meriac/openbeacon-ng/firmware/nRF51/tag-proximity/src/main.c

/***************************************************************
 *
 * OpenBeacon.org - nRF51 Main Entry
 *
 * Copyright 2013 Milosch Meriac <meriac@openbeacon.de>
 *
 ***************************************************************

 This file is part of the OpenBeacon.org active RFID firmware

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
*/
#include <openbeacon.h>

#include <acc.h>
#include <adc.h>
#include <log.h>
#include <radio.h>
#include <timer.h>

static int8_t g_tag_angle;

int8_t tag_angle(void)
{
	return g_tag_angle;
}

static void blink(uint8_t times)
{
	while(times--)
	{
		nrf_gpio_pin_set(CONFIG_LED_PIN);
		timer_wait(MILLISECONDS(1));
		nrf_gpio_pin_clear(CONFIG_LED_PIN);
		timer_wait(MILLISECONDS(499));
	}
}

void halt(uint8_t times)
{
	while(TRUE)
	{
		blink(times);
		timer_wait(SECONDS(3));
	}
}

static void run_mode_beacon(uint32_t tag_id)
{
	int i;
	bool do_blink;

	/* start radio */
	radio_init(tag_id);
	debug_printf("- Start radio\n\r");

	/* power down USART */
	uart_power(FALSE);

	/* turn off LED to indicate operation */
	nrf_gpio_pin_clear(CONFIG_LED_PIN);

	/* enter main loop */
	i = 0;
	do_blink = false;
	while(TRUE)
	{
		/* get tag angle once per second */
		acc_magnitude(&g_tag_angle);
		timer_wait(MILLISECONDS(1000));

		/* process log entries */
		if(log_process())
			do_blink = true;

		/* blink every 5 seconds */
		if(i<5)
			i++;
		else
		{
			i = 0;
			nrf_gpio_pin_set(CONFIG_LED_PIN);
			timer_wait(MILLISECONDS(1));
			nrf_gpio_pin_clear(CONFIG_LED_PIN);

			/* check whether to indicate logging of data */
			if(do_blink)
			{
				do_blink = false;
				timer_wait(MILLISECONDS(100));
				nrf_gpio_pin_set(CONFIG_LED_PIN);
				timer_wait(MILLISECONDS(1));
				nrf_gpio_pin_clear(CONFIG_LED_PIN);
			}
		}
	}
}

void main_entry(void)
{
	int voltage;
	uint32_t tag_id;

	/* enabled LED output */
	nrf_gpio_cfg_output(CONFIG_LED_PIN);
	nrf_gpio_pin_set(CONFIG_LED_PIN);

	/* enabled input pin */
	nrf_gpio_cfg_input(CONFIG_SWITCH_PIN, NRF_GPIO_PIN_NOPULL);

	/* initialize UART */
	uart_init();

	/* start timer */
	timer_init();

	/* calculate tag ID from NRF_FICR->DEVICEID */
	tag_id = crc32((void*)&NRF_FICR->DEVICEID, sizeof(NRF_FICR->DEVICEID));
#if defined(MARKER_TAG_NEAR) || defined(MARKER_TAG_FAR)
	tag_id |= MARKER_TAG_BIT;
#else /*MARKER_TAG*/
	tag_id &= MARKER_TAG_BIT-1;
#endif/*MARKER_TAG*/
	debug_printf("\n\rInitializing Tag[%08X] v" PROGRAM_VERSION " @24%02iMHz ...\n\r",
		tag_id,
		CONFIG_TRACKER_CHANNEL);

	/* initialize ADC battery voltage measurements */
	adc_init();
	voltage = (int)adc_bat_sync() * 100;
	debug_printf("- Supply voltage of %imV\n\r", voltage);

	/* initialize external flash */
	if(log_init(tag_id))
		halt(2);

	/* initialize accelerometer */
	if(acc_init())
		halt(3);

	/* for voltages above 3.2V assume to be in reader */
	if(voltage >= 3200)
		log_dump(tag_id);
	else
		run_mode_beacon(tag_id);
}
