meriac/openbeacon-ng/firmware/nRF51/tag-proximity/src/radio.c

/***************************************************************
 *
 * OpenBeacon.org - nRF51 2.4GHz Radio Routines
 *
 * Copyright 2013 Milosch Meriac <meriac@openbeacon.de>
 *
 ***************************************************************

 This file is part of the OpenBeacon.org active RFID firmware

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
*/
#include <openbeacon.h>
#include <main.h>
#include <radio.h>
#include <adc.h>
#include <aes.h>
#include <rng.h>
#include <log.h>
#include <timer.h>

/* set proximity power */
#ifdef MARKER_TAG_FAR
#  define PX_POWER 4
#  define PX_POWER_VALUE RADIO_TXPOWER_TXPOWER_Pos4dBm
#elif  MARKER_TAG_NEAR
#  define PX_POWER -16
#  define PX_POWER_VALUE RADIO_TXPOWER_TXPOWER_Neg16dBm
#else/*PROX_TAG*/
#  define PROX_TAG
#  define PX_POWER -20
#  define PX_POWER_VALUE RADIO_TXPOWER_TXPOWER_Neg20dBm
#endif/*MARKER_TAG*/

#define RXTX_BASELOSS -4.0
#define BALUN_INSERT_LOSS -2.25
#define BALUN_RETURN_LOSS -10.0
#define ANTENNA_GAIN 0.5
#define RX_LOSS ((RXTX_BASELOSS/2.0)+BALUN_RETURN_LOSS+ANTENNA_GAIN)
#define TX_LOSS ((RXTX_BASELOSS/2.0)+BALUN_INSERT_LOSS+ANTENNA_GAIN)

static volatile uint32_t g_time, g_pkt_tracker_ticks;
static volatile uint16_t g_ticks_offset;
static volatile uint8_t g_request_tx;
static uint8_t g_listen_ratio;
static uint8_t g_nrf_state;
static int8_t g_rssi;
static uint8_t g_button_pressed;

static TBeaconNgProx g_pkt_prox ALIGN4;
static uint8_t g_pkt_prox_enc[sizeof(g_pkt_prox)] ALIGN4;

static TBeaconNgProx g_pkt_prox_rx ALIGN4;
static uint8_t g_pkt_prox_rx_enc[sizeof(g_pkt_prox_rx)] ALIGN4;

static TBeaconNgTracker g_pkt_tracker ALIGN4;
static uint8_t g_pkt_tracker_enc[sizeof(g_pkt_tracker)] ALIGN4;

/* don't start DC/DC converter for voltages below 2.3V */
#define NRF_DCDC_STARTUP_VOLTAGE 23

#define NRF_MAC_SIZE 5UL
#define NRF_PROX_SIZE sizeof(TBeaconNgProx)
#define NRF_TRACKER_SIZE sizeof(TBeaconNgTracker)

#define NRF_STATE_IDLE           0
#define NRF_STATE_TX_PROX        1
#define NRF_STATE_RX_PROX        2
#define NRF_STATE_RX_PROX_PACKET 3
#define NRF_STATE_RX_PROX_BLINK  4
#define NRF_STATE_TX_TRACKER     5

#define RADIO_TRACKER_TXADDRESS 1
#define RADIO_TRACKER_TXPOWER (RADIO_TXPOWER_TXPOWER_Pos4dBm << RADIO_TXPOWER_TXPOWER_Pos)
#define RADIO_TRACKER_PCNF1 \
		(RADIO_PCNF1_WHITEEN_Disabled << RADIO_PCNF1_WHITEEN_Pos) |\
		(RADIO_PCNF1_ENDIAN_Big       << RADIO_PCNF1_ENDIAN_Pos)  |\
		((NRF_MAC_SIZE-1UL)           << RADIO_PCNF1_BALEN_Pos)   |\
		(NRF_TRACKER_SIZE             << RADIO_PCNF1_STATLEN_Pos) |\
		(NRF_TRACKER_SIZE             << RADIO_PCNF1_MAXLEN_Pos)

#define RADIO_PROX_TXADDRESS 0
#define RADIO_PROX_TXPOWER (PX_POWER_VALUE << RADIO_TXPOWER_TXPOWER_Pos)
#define RADIO_PROX_PCNF1 \
		(RADIO_PCNF1_WHITEEN_Enabled  << RADIO_PCNF1_WHITEEN_Pos) |\
		(RADIO_PCNF1_ENDIAN_Big       << RADIO_PCNF1_ENDIAN_Pos)  |\
		((NRF_MAC_SIZE-1UL)           << RADIO_PCNF1_BALEN_Pos)   |\
		(NRF_PROX_SIZE                << RADIO_PCNF1_STATLEN_Pos) |\
		(NRF_PROX_SIZE                << RADIO_PCNF1_MAXLEN_Pos)

void RTC0_IRQ_Handler(void)
{
	uint32_t delta_t;

	/* run every second */
	if(NRF_RTC0->EVENTS_COMPARE[0])
	{
		/* acknowledge event */
		NRF_RTC0->EVENTS_COMPARE[0] = 0;

		/* re-trigger in one second */
		NRF_RTC0->CC[0]+= LF_FREQUENCY;

		/* increment time */
		g_time++;

		/* decrement button timer if needed */
		if(g_button_pressed)
			g_button_pressed--;

		/* schedule tracker TX */
		if(!g_request_tx)
			/* wait for random(2^5) slots */
			g_request_tx = rng(5);

		/* measure battery voltage once per second */
		adc_start();
	}

	if(NRF_RTC0->EVENTS_COMPARE[1])
	{
		/* acknowledge event */
		NRF_RTC0->EVENTS_COMPARE[1] = 0;

		/* re-trigger next RX/TX-slot */
		delta_t =
			CONFIG_PROX_SPACING -
			(1<<(CONFIG_PROX_SPACING_RNG_BITS-1)) +
			rng(CONFIG_PROX_SPACING_RNG_BITS);
		NRF_RTC0->CC[1] = NRF_RTC0->COUNTER + delta_t;

		/* start HF crystal oscillator */
		NRF_CLOCK->TASKS_HFCLKSTART = 1;

#ifdef  PROX_TAG
		/* listen every CONFIG_PROX_LISTEN_RATIO slots */
		g_listen_ratio++;
#endif/*PROX_TAG*/
		if(g_listen_ratio<CONFIG_PROX_LISTEN_RATIO)
			g_nrf_state = NRF_STATE_TX_PROX;
		else
		{
			g_listen_ratio = 0;
			g_nrf_state = NRF_STATE_RX_PROX;

			/* only start DC/DC converter for
			 * RX & higher battery voltages */
			if(adc_bat()>=NRF_DCDC_STARTUP_VOLTAGE)
			{
				/* start DC-DC converter */
				NRF_POWER->DCDCEN = (
					(POWER_DCDCEN_DCDCEN_Enabled << POWER_DCDCEN_DCDCEN_Pos)
				);
			}
		}
	}

	/* listen for CONFIG_PROX_WINDOW_MS every second */
	if(NRF_RTC0->EVENTS_COMPARE[2])
	{
		/* acknowledge event */
		NRF_RTC0->EVENTS_COMPARE[2] = 0;

		/* stop HF clock */
		NRF_CLOCK->TASKS_HFCLKSTOP = 1;

#ifdef  PROXIMITY_BLINK
		if(g_nrf_state == NRF_STATE_RX_PROX_BLINK)
		{
			g_nrf_state = NRF_STATE_IDLE;
			/* light LED */
			nrf_gpio_pin_set(CONFIG_LED_PIN);
			/* retrigger LED blink */
			NRF_RTC0->CC[2] = NRF_RTC0->COUNTER + MILLISECONDS(1);
		}
		else
#endif/*PROXIMITY_BLINK*/
		{
			/* set next state */
			g_nrf_state = NRF_STATE_IDLE;
			/* stop radio */
			NRF_RADIO->TASKS_DISABLE = 1;
			/* disable DC-DC converter */
			NRF_POWER->DCDCEN = 0;
			/* disable LED */
			nrf_gpio_pin_clear(CONFIG_LED_PIN);
		}
	}
}

void POWER_CLOCK_IRQ_Handler(void)
{
	/* always transmit proximity packet */
	if(NRF_CLOCK->EVENTS_HFCLKSTARTED)
	{
		/* acknowledge event */
		NRF_CLOCK->EVENTS_HFCLKSTARTED = 0;

		/* update proximity time */
		g_pkt_prox.p.prox.epoch = g_time;
		g_pkt_prox.p.prox.ticks = NRF_RTC0->COUNTER;

		/* encrypt data */
		aes_encr(
			&g_pkt_prox,
			&g_pkt_prox_enc,
			sizeof(g_pkt_prox_enc),
			CONFIG_SIGNATURE_SIZE
		);

		/* set first packet pointer */
		NRF_RADIO->PACKETPTR = (uint32_t)&g_pkt_prox_enc;
		/* transmit proximity packet */
		NRF_RADIO->TASKS_TXEN = 1;
	}
}

static void radio_on_prox_packet(void)
{
	int i;
	TBeaconNgSighting *slot;

	/* ignore unknown protocols */
	if(g_pkt_prox_rx.proto != RFBPROTO_BEACON_NG_PROX)
		return;

	/* ignore replayed packets from myself */
	if(g_pkt_prox_rx.p.prox.uid == g_pkt_prox.p.prox.uid)
		return;

	/* store sighting in external flash */
	log_sighting(
		g_time,
		g_pkt_prox_rx.p.prox.epoch,
		g_pkt_prox_rx.p.prox.uid,
		g_rssi,
		tag_angle()
	);

	/* remember proximity sighting */
	slot = g_pkt_tracker.p.sighting;
	for(i=0; i<CONFIG_SIGHTING_SLOTS; i++)
	{
		/* ignore older readings */
		if(slot->uid==g_pkt_prox_rx.p.prox.uid)
			break;

		/* use first free entry */
		if(!slot->uid)
		{
			slot->uid = g_pkt_prox_rx.p.prox.uid;
			slot->rx_power = g_rssi;
			break;
		}

		slot++;
	}
}

void RADIO_IRQ_Handler(void)
{
	uint32_t ticks;

	if(NRF_RADIO->EVENTS_DISABLED)
	{
		/* acknowledge event */
		NRF_RADIO->EVENTS_DISABLED = 0;

		/* process state machine */
		switch(g_nrf_state)
		{
			case NRF_STATE_RX_PROX:
			{
				/* set next state */
				g_nrf_state = NRF_STATE_RX_PROX_PACKET;
				/* reset rssi measurement */
				g_rssi = 0;
				/* set first packet pointer */
				NRF_RADIO->PACKETPTR = (uint32_t)&g_pkt_prox_rx_enc;
				/* start listening */
				NRF_RADIO->TASKS_RXEN = 1;

				/* retrigger listening stop */
				NRF_RTC0->CC[2] = NRF_RTC0->COUNTER + CONFIG_PROX_LISTEN;
				break;
			}

			case NRF_STATE_TX_PROX:
			{
				/* set default next state */
				g_nrf_state = NRF_STATE_IDLE;
				/* transmit pending tracker packets in a random slot */
				if(g_request_tx)
				{
					g_request_tx--;
					if(!g_request_tx)
						/* divert to tracker TX state */
						g_nrf_state = NRF_STATE_TX_TRACKER;
				}

				if(g_nrf_state == NRF_STATE_TX_TRACKER)
				{
					/* reconfigure radio for tracker TX */
					NRF_RADIO->FREQUENCY = CONFIG_TRACKER_CHANNEL;
					NRF_RADIO->TXPOWER = RADIO_TRACKER_TXPOWER;
					NRF_RADIO->TXADDRESS = RADIO_TRACKER_TXADDRESS;
					NRF_RADIO->PCNF1 = RADIO_TRACKER_PCNF1;

					/* update tracker packet */
					if(g_pkt_tracker.p.sighting[0].uid)
						g_pkt_tracker.proto = RFBPROTO_BEACON_NG_SIGHTING;
					else
					{
						g_pkt_tracker.proto = RFBPROTO_BEACON_NG_STATUS;
						g_pkt_tracker.p.status.rx_loss = (int16_t)((RX_LOSS*100)+0.5);
						g_pkt_tracker.p.status.tx_loss = (int16_t)((TX_LOSS*100)+0.5);
						g_pkt_tracker.p.status.px_power = (int16_t)((PX_POWER*100)+0.5);
						g_pkt_tracker.p.status.ticks = NRF_RTC0->COUNTER + g_ticks_offset + g_pkt_tracker_ticks;
					}
					g_pkt_tracker.epoch = g_time;
					g_pkt_tracker.angle = tag_angle();
					g_pkt_tracker.voltage = adc_bat();

					/* propagate button press if needed */
					if(g_button_pressed)
						g_pkt_tracker.proto |= RFBPROTO_PROTO_BUTTON;

					/* measure encryption time */
					ticks = NRF_RTC0->COUNTER;

					/* encrypt packet */
					aes_encr(
						&g_pkt_tracker,
						&g_pkt_tracker_enc,
						sizeof(g_pkt_tracker_enc),
						CONFIG_SIGNATURE_SIZE
					);
					/* set first packet pointer */
					NRF_RADIO->PACKETPTR = (uint32_t)&g_pkt_tracker_enc;
					/* start tracker TX */
					NRF_RADIO->TASKS_TXEN = 1;

					/* update encryption time */
					g_pkt_tracker_ticks = NRF_RTC0->COUNTER - ticks;
				}
				else
				{
					/* stop HF clock */
					NRF_CLOCK->TASKS_HFCLKSTOP = 1;
					/* disable DC-DC converter */
					NRF_POWER->DCDCEN = 0;
				}
				break;
			}

			case NRF_STATE_TX_TRACKER:
			{
				/* set next state */
				g_nrf_state = NRF_STATE_IDLE;

				/* reconfigure radio back to proximity */
				NRF_RADIO->FREQUENCY = CONFIG_PROX_CHANNEL;
				NRF_RADIO->TXPOWER = RADIO_PROX_TXPOWER;
				NRF_RADIO->TXADDRESS = RADIO_PROX_TXADDRESS;
				NRF_RADIO->PCNF1 = RADIO_PROX_PCNF1;

				/* stop HF clock */
				NRF_CLOCK->TASKS_HFCLKSTOP = 1;
				/* disable DC-DC converter */
				NRF_POWER->DCDCEN = 0;

				/* confirm tracker transmission */
				memset(&g_pkt_tracker.p, 0, sizeof(g_pkt_tracker.p));
				g_request_tx = FALSE;
				break;
			}
		}
	}

	if(NRF_RADIO->EVENTS_END)
	{
		/* acknowledge event */
		NRF_RADIO->EVENTS_END = 0;

		/* received packet */
		if(	(g_nrf_state == NRF_STATE_RX_PROX_PACKET) && 
			(NRF_RADIO->CRCSTATUS == 1) )
		{
			/* measure decryption time */
			ticks = NRF_RTC0->COUNTER;

			/* decrypt and verify packet */
			if(!aes_decr(
				&g_pkt_prox_rx_enc,
				&g_pkt_prox_rx,
				sizeof(g_pkt_prox_rx),
				CONFIG_SIGNATURE_SIZE))
			{
				g_nrf_state = NRF_STATE_RX_PROX_BLINK;
				radio_on_prox_packet();
			}
		}
	}

	if(NRF_RADIO->EVENTS_RSSIEND)
	{
		g_rssi = -((int8_t)NRF_RADIO->RSSISAMPLE);

		/* acknowledge event */
		NRF_RADIO->EVENTS_RSSIEND = 0;

		/* disable RSSI measurement */
		NRF_RADIO->TASKS_RSSISTOP = 1;
	}
}

void GPIOTE_IRQ_Handler(void)
{
	if(NRF_GPIOTE->EVENTS_IN[0])
	{
		NRF_GPIOTE->EVENTS_IN[0] = 0;

		g_button_pressed = CONFIG_BUTTON_DURATION_SECONDS;
	}
}

void radio_init(uint32_t uid)
{
	/* reset variables */
	g_time = 0;
	g_pkt_tracker_ticks = 0;
	g_ticks_offset = 0;
	g_listen_ratio = 0;
	g_nrf_state = 0;
	g_request_tx = 0;
	g_rssi = 0;
	g_button_pressed = 0;

	/* initialize proximity packet */
	memset(&g_pkt_prox, 0, sizeof(g_pkt_prox));
	g_pkt_prox.proto = RFBPROTO_BEACON_NG_PROX;
	g_pkt_prox.p.prox.uid = uid;

	/* initialize tracker packet */
	memset(&g_pkt_tracker, 0, sizeof(g_pkt_tracker));
	g_pkt_tracker.tx_power = 4;
	g_pkt_tracker.uid = uid;

	/* start random number genrator */
	rng_init();
	/* initialize AES encryption engine */
	aes_init(uid);

	/* setup default radio settings for proximity mode */
	NRF_RADIO->MODE = RADIO_MODE_MODE_Nrf_2Mbit << RADIO_MODE_MODE_Pos;
	NRF_RADIO->FREQUENCY = CONFIG_PROX_CHANNEL;
	NRF_RADIO->TXPOWER = RADIO_PROX_TXPOWER;
	NRF_RADIO->TXADDRESS = RADIO_PROX_TXADDRESS;
	NRF_RADIO->PCNF1 = RADIO_PROX_PCNF1;
	/* generic radio setup */
	NRF_RADIO->PREFIX0 = 0x46D7UL;
	NRF_RADIO->BASE0 = 0xEA8AF0B1UL;
	NRF_RADIO->BASE1 = 0xCC864569UL;
	NRF_RADIO->RXADDRESSES = 1;
	NRF_RADIO->PCNF0 = 0x0;
	NRF_RADIO->CRCCNF = (RADIO_CRCCNF_LEN_One << RADIO_CRCCNF_LEN_Pos);
	NRF_RADIO->CRCINIT = 0xFFUL;
	NRF_RADIO->CRCPOLY = 0x107UL;
	NRF_RADIO->SHORTS = (
		(RADIO_SHORTS_READY_START_Enabled       << RADIO_SHORTS_READY_START_Pos)       |
		(RADIO_SHORTS_END_DISABLE_Enabled       << RADIO_SHORTS_END_DISABLE_Pos)       |
		(RADIO_SHORTS_ADDRESS_RSSISTART_Enabled << RADIO_SHORTS_ADDRESS_RSSISTART_Pos) |
		(RADIO_SHORTS_DISABLED_RSSISTOP_Enabled << RADIO_SHORTS_DISABLED_RSSISTOP_Pos)
	);
	NRF_RADIO->INTENSET = (
		(RADIO_INTENSET_RSSIEND_Enabled         << RADIO_INTENSET_RSSIEND_Pos)  |
		(RADIO_INTENSET_DISABLED_Enabled        << RADIO_INTENSET_DISABLED_Pos) |
		(RADIO_INTENSET_END_Enabled             << RADIO_INTENSET_END_Pos)
	);
	NVIC_SetPriority(RADIO_IRQn, IRQ_PRIORITY_RADIO);
	NVIC_EnableIRQ(RADIO_IRQn);

	/* setup HF-clock IRQ */
	NRF_CLOCK->INTENSET = (
		(CLOCK_INTENSET_HFCLKSTARTED_Enabled << CLOCK_INTENSET_HFCLKSTARTED_Pos)
	);
	NVIC_SetPriority(POWER_CLOCK_IRQn, IRQ_PRIORITY_POWER_CLOCK);
	NVIC_EnableIRQ(POWER_CLOCK_IRQn);

	/* setup radio timer */
	NRF_RTC0->TASKS_STOP = 1;
	NRF_RTC0->COUNTER = 0;
	NRF_RTC0->PRESCALER = 0;
	NRF_RTC0->CC[0] = LF_FREQUENCY;
	NRF_RTC0->CC[1] = LF_FREQUENCY*2;
	NRF_RTC0->CC[2] = 0;
	NRF_RTC0->INTENSET = (
		(RTC_INTENSET_COMPARE0_Enabled   << RTC_INTENSET_COMPARE0_Pos) |
		(RTC_INTENSET_COMPARE1_Enabled   << RTC_INTENSET_COMPARE1_Pos) |
		(RTC_INTENSET_COMPARE2_Enabled   << RTC_INTENSET_COMPARE2_Pos)
	);
	NVIC_SetPriority(RTC0_IRQn, IRQ_PRIORITY_RTC0);
	NVIC_EnableIRQ(RTC0_IRQn);
	NRF_RTC0->TASKS_START = 1;

	/* configure button IRQ handler */
	nrf_gpiote_event_config(0, CONFIG_SWITCH_PIN, GPIOTE_CONFIG_POLARITY_HiToLo);
	NRF_GPIOTE->INTENSET = (
		(GPIOTE_INTENSET_IN0_Enabled     << GPIOTE_INTENSET_IN0_Pos)
	);
	NVIC_SetPriority(GPIOTE_IRQn, IRQ_PRIORITY_GPIOTE);
	NVIC_EnableIRQ(GPIOTE_IRQn);
}
