meriac/openbeacon-ng/firmware/nRF51/tag-mischief/inc/db.h

#ifndef __DB_H__
#define __DB_H__

const char g_prefix_cal[] = "\0Aaroni\0Abapi\0Abbati\0Abiologi\0Abioti"
	"\0Ablepti\0Academi\0Acaly\0Acanoni\0Achroni\0Acousti\0Acriti\0Acrobati"
	"\0Acroni\0Acrony\0Acrosti\0Actini\0Adami\0Adamiti\0Aeri\0Aerologi"
	"\0Aeromedi\0Aeronomi\0Aestheti\0Afo\0Agnati\0Agnomi\0Agnosti\0Agonisti"
	"\0Agresti\0Agrologi\0Agronomi\0Ahistori\0Albiti\0Alchemi\0Algebrai"
	"\0Algologi\0Aliturgi\0Allegori\0Allotypi\0Aloeti\0Alogi\0Amethodi\0Ami"
	"\0Ammonia\0Ammoni\0Anagogi\0Analepti\0Analogi\0Analyti\0Anaphori\0Anarchi"
	"\0Anareti\0Anatomi\0Anecdoti\0Angeli\0Angeli\0Animasti\0Anisocer\0Anovesi"
	"\0Antarcti\0Antecae\0Antefur\0Anthropi\0Anti\0Anticyni\0Antidoti"
	"\0Antilogi\0Antimedi\0Antimusi\0Antinomi\0Antiradi\0Antitypi\0Apagogi"
	"\0Apatheti\0Api\0Apodicti\0Apoliti\0Apologi\0Apomicti\0Aporeti\0Apostati"
	"\0Apostoli\0Apothe\0Apotihe\0Apozemi\0Appendi\0Apsychi\0Aquati\0Arbori"
	"\0Archai\0Archdu\0Archi\0Archradi\0Archras\0Areologi\0Arhythmi\0Aromati"
	"\0Arrythmi\0Arseni\0Arthriti\0Artisti\0Arythmi\0Asceti\0Asciti\0Asiati"
	"\0Aspheri\0Astheni\0Asthmati\0Asyllabi\0Asymboli\0Atechni\0Atheisti"
	"\0Athleti\0Atmologi\0Atomi\0Atomisti\0Atti\0Atypi\0Auli\0Autarchi"
	"\0Autarki\0Authenti\0Autologi\0Automati\0Autonomi\0Autopsi\0Autopti"
	"\0Auxeti\0Axiologi\0Axiomati\0Baaliti\0Bacchi\0Balladi\0Balsami\0Ban"
	"\0Bandboxi\0Barbari\0Baroneti\0Basili\0Beatifi\0Belli\0Beras\0Beyli"
	"\0Bibli\0Bibli\0Biconi\0Bicycli\0Bifo\0Bifur\0Biochemi\0Biologi\0Biomedi"
	"\0Biometri\0Bionomi\0Biophysi\0Biostati\0Bioti\0Biunivo\0Bivo\0Bo"
	"\0Bombasti\0Botani\0Brahmani\0Brahmini\0Bryologi\0Buc\0Bucoli\0Bun"
	"\0Cachecti\0Cacodoxi\0Cacologi\0Cae\0\0\0Calendri\0Calorifi\0Canoni\0Cara"
	"\0Cardia\0Caru\0Casuisti\0Catalogi\0Catalyti\0Categori\0Catharti\0Cathodi"
	"\0Catholi\0Catoptri\0Causidi\0Causti\0Ce\0Cenobiti\0Centoni\0Centri\0Cer"
	"\0Cervi\0Cetologi\0Chaldai\0Chaoti\0Chemi\0Chemurgi\0Cherubi\0Chimeri"
	"\0Chiragri\0Chirurgi\0Choplogi\0Chromati\0Chroni\0Cinemati\0Civi\0Classi"
	"\0Cleri\0Climacti\0Climati\0Clini\0Cloa\0Coc\0Codi\0Coe\0Coenosar"
	"\0Cognati\0Coli\0Collo\0Coloni\0Comedi\0Cometi\0Comi\0Confo\0Coni"
	"\0Conoidi\0Contrafo\0Conventi\0Coradi\0Corti\0Cosmeti\0Cosmi\0Costoapi"
	"\0Cou\0Coverti\0Coxcombi\0Coxcomi\0Criti\0Cryologi\0Crypti\0Cubi\0Curati"
	"\0Cycli\0Cycloni\0Cylindri\0Cyni\0Cyni\0Cytologi\0Dandia\0Darwini\0Davidi"
	"\0De\0Deicti\0Deifi\0Deisti\0Demagogi\0Demiurgi\0Demologi\0Demonia"
	"\0Demoni\0Dendriti\0Denti\0Dentisti\0Dephycer\0Despoti\0Dexteri\0Diabeti"
	"\0Diaboli\0Diacriti\0Dialecti\0Dialogi\0Diametri\0Dianoeti\0Diaphoni"
	"\0Diatoni\0Didacti\0Dieteti\0Dieti\0Dilogi\0Dini\0Dionysia\0Dioptri"
	"\0Diphycer\0Diplococ\0Dis\0Dithe\0Diureti\0Dochmia\0Dogmati\0Domi\0Domini"
	"\0Dori\0Dorsoapi\0Doxologi\0Dramati\0Dromi\0Dropsi\0Druidi\0Du\0Du\0Dunci"
	"\0Dyarchi\0Dynami\0Dynamiti\0Dynasti\0Dysgeni\0Dyspepti\0Eccentri"
	"\0Eclecti\0Eclipti\0Ecologi\0Economi\0Ecstati\0Ecumeni\0Egoisti\0Egomania"
	"\0Egotisti\0Eisegeti\0Electri\0Elegia\0Elenchi\0Elenchti\0Elencti"
	"\0Ellipti\0Emeti\0Emphati\0Empiri\0Empyri\0Encliti\0Encycli\0Endemi"
	"\0Endostra\0Endothe\0Energeti\0Energi\0Enigmati\0Enneati\0Enologi\0Entifi"
	"\0Entomi\0Entopi\0Entopti\0Epi\0Epicorti\0Epicycli\0Epidemi\0Epidermi"
	"\0Epidicti\0Epifo\0Epilepti\0Epilogi\0Epiphyti\0Episodi\0Epistoli"
	"\0Epitaphi\0Epithe\0Epitheti\0Epitomi\0Equiradi\0Equivo\0Eremiti\0Eri"
	"\0Eristi\0Eroti\0Errati\0Eruditi\0Esoteri\0Essayi\0Esseni\0Estheti"
	"\0Etheri\0Ethi\0Ethni\0Ethologi\0Etiologi\0Etypi\0Eucti\0Eugeni\0Eulogi"
	"\0Euphoni\0Eurythmi\0Evangeli\0Evangeli\0Excentri\0Exegeti\0Exoteri"
	"\0Exothe\0Extrabuc\0Extrafo\0Extrathe\0Extrinsi\0Extropi\0Exzodia\0Fae"
	"\0Falsidi\0Fanati\0Fanci\0Fantasti\0Farci\0Fatidi\0Fau\0Faunisti\0Fe"
	"\0Fili\0Fini\0Fis\0Fisti\0Flamini\0Fo\0Forensi\0Forinse\0Forni\0Freneti"
	"\0Fris\0Fur\0Galeni\0Galeni\0Galvani\0Gematri\0Gemologi\0Generi\0Genesia"
	"\0Geneti\0Genotypi\0Geochemi\0Geodesi\0Geodeti\0Geogoni\0Geologi"
	"\0Geomanti\0Geomedi\0Geometri\0Geophysi\0Geoponi\0Georgi\0Geoti\0Germani"
	"\0Gerocomi\0Gesti\0Giganti\0Globi\0Glypti\0Gnathoni\0Gnomi\0Gnomoni"
	"\0Gnosti\0Goeti\0Gonococ\0Gonothe\0Graduati\0Grammati\0Graniti\0Graphi"
	"\0Gromati\0Gymnasti\0Gymni\0Haccu\0Haggadi\0Halieuti\0Hallu\0Hapti"
	"\0Harmonia\0Harmoni\0Harpsi\0Haruspi\0Hebrai\0Hecti\0Hedoni\0Hegemoni"
	"\0Helia\0Heli\0Hepati\0Heraldi\0Hereti\0Hermeti\0Hermiti\0Heroi\0Hexagoni"
	"\0Hiberni\0Hierati\0Hierurgi\0Histori\0Hobbisti\0Holothe\0Homeri"
	"\0Homileti\0Homocer\0Homologi\0Homotypi\0Honorifi\0Horologi\0Hydropi"
	"\0Hydrothe\0Hydroti\0Hygieni\0Hylarchi\0Hylegia\0Hymnodi\0Hyperfo"
	"\0Hypothe\0Hypotypi\0Hysteri\0Iambi\0Iatri\0Iconi\0Icteri\0Idealogi"
	"\0Identi\0Ideogeni\0Ideologi\0Idiomati\0Idioti\0Idolatri\0Idylli\0Ileocae"
	"\0Ileoce\0Illo\0Illogi\0Immetri\0Immusi\0Impoliti\0Impracti\0Indexi\0Indi"
	"\0Inethi\0Infideli\0Infrabuc\0Inimi\0Inorgani\0Interdis\0Interlo"
	"\0Interpli\0Intervo\0Intrabuc\0Intrathe\0Intrinsi\0Ioni\0Ireni\0Iridi"
	"\0Ironi\0Irrubri\0Isagogi\0Isia\0Ismati\0Isocer\0Isomeri\0Isometri"
	"\0Isostati\0Isotypi\0Itali\0Ja\0Jacobini\0Jacobiti\0Jebusiti\0Jesuiti"
	"\0Jesuiti\0Judai\0Judai\0Judgmati\0Judi\0Jun\0Juridi\0Juristi\0K"
	"\0Kinemati\0Kineti\0Laconi\0Lactifi\0Lai\0Lapidifi\0Largifi\0Latreuti"
	"\0Leptocer\0Lethargi\0Levirati\0Leviti\0Leviti\0Lexi\0Lexologi\0Liturgi"
	"\0Lo\0Logi\0Logisti\0Lophocer\0Lubri\0Lumbri\0Lunati\0Luper\0Luper"
	"\0Lustri\0Lymphati\0Lyri\0Macaroni\0Magesti\0Magi\0Magneti\0Magnifi"
	"\0Maieuti\0Majesti\0Malefi\0Mammonia\0Mania\0Masoreti\0Matri\0Matrilo"
	"\0Mechani\0Medi\0Melodi\0Menis\0Mephiti\0Mer\0Mesarai\0Mes\0Mesiobuc"
	"\0Mesmeri\0Mesocae\0Mesofur\0Mesologi\0Metaboli\0Metaethi\0Metalli"
	"\0Metalogi\0Metatati\0Meteori\0Methodi\0Meti\0Metonymi\0Metri\0Mexi\0Mez"
	"\0Miasmati\0Micrococ\0Micrurgi\0Mimeti\0Mimi\0Mirifi\0Mis\0Mishni"
	"\0Misogyni\0Missati\0Mnemoni\0Monadi\0Monarchi\0Monasti\0Monisti\0Monodi"
	"\0Monologi\0Monopti\0Monothe\0Monotoni\0Monotypi\0Morbifi\0Morologi"
	"\0Mosai\0Mosai\0Multifo\0Multivo\0Musi\0Mycologi\0Myologi\0Myophysi"
	"\0Myopi\0Mysta\0Mysti\0Mythi\0Nabobi\0Naologi\0Narcoti\0Narthe\0Nasobuc"
	"\0Nasologi\0Nauti\0Neocorti\0Neologi\0Neoteri\0Neotropi\0Neotropi"
	"\0Nephriti\0New\0Nimrodi\0Nineviti\0Noachi\0Noctilu\0Nodi\0Noemati"
	"\0Nomadi\0Nomologi\0Nonatomi\0Nonchemi\0Noncleri\0Nonclini\0Noncomi"
	"\0Noncorti\0Noncriti\0Noncycli\0Nonepi\0Nonethi\0Nonethni\0Nonfarci"
	"\0Nonfis\0Nonfo\0Nongesti\0Nonheroi\0Nonireni\0Nonironi\0Nonlo\0Nonlogi"
	"\0Nonlyri\0Nonmedi\0Nonmetri\0Nonmusi\0Nonmysti\0Nonmythi\0Nonnauti"
	"\0Nonopti\0Nonphysi\0Nonradi\0Nonsensi\0Nonstoi\0Nonsurgi\0Nontacti"
	"\0Nontragi\0Nontropi\0Nontypi\0Nonverti\0Nonvo\0Nonvorti\0Nonzodia"
	"\0Noologi\0Nosologi\0Nover\0Nu\0Numeri\0Nymphi\0Obconi\0Obelis\0Obstetri"
	"\0Odometri\0Oecodomi\0Oecologi\0Oecumeni\0Oenologi\0Oligisti\0Ologi"
	"\0Omnifo\0Oncologi\0Onomasti\0Ontologi\0Oologi\0Oothe\0Operati\0Opti"
	"\0Optologi\0Oratori\0Orbi\0Organi\0Orgiasti\0Origeni\0Orologi\0Orphi"
	"\0Orphi\0Orthoepi\0Otologi\0Overlogi\0Ovidu\0Ovologi\0Oxytoni\0Pacifi"
	"\0Pagani\0Pamphysi\0Pancrati\0Panegyri\0Pangyri\0Pani\0Panlogi\0Panopti"
	"\0Panorami\0Pansophi\0Pantropi\0Paparchi\0Papisti\0Paraboli\0Paradisi"
	"\0Paradoxi\0Paragogi\0Paraliti\0Paralogi\0Paralyti\0Paramedi\0Parasiti"
	"\0Paratypi\0Paravesi\0Paregori\0Pareneti\0Parfo\0Parhelia\0Parodi"
	"\0Parsoni\0Pas\0Pas\0Patheti\0Patrilo\0Patrioti\0Patristi\0Pau\0Pedagogi"
	"\0Pedanti\0Pedo\0Pedologi\0Penologi\0Pepti\0Periapi\0Pericae\0Perice"
	"\0Periodi\0Perisar\0Perivesi\0Phalli\0Phantomi\0Pharaoni\0Pharisai"
	"\0Pharma\0Phengiti\0Pho\0Phoneti\0Phreneti\0Phthisi\0Physi\0Pi\0Pictori"
	"\0Pietisti\0Pindari\0Pirati\0Pitta\0Plagiari\0Plasmati\0Platoni\0Plethori"
	"\0Pleuriti\0Pli\0Plotini\0Pneumati\0Podagri\0Podi\0Podothe\0Poeti\0Polemi"
	"\0Politi\0Polli\0Pollini\0Polygami\0Polytopi\0Polytypi\0Pomologi\0Pontifi"
	"\0Poristi\0Posologi\0Postbuc\0Postcae\0Postce\0Postfur\0Posti\0Postvesi"
	"\0Practi\0Pragmati\0Prebibli\0Prebuc\0Prechemi\0Precleri\0Preclini"
	"\0Precloa\0Precosmi\0Precriti\0Precyni\0Prelati\0Prelexi\0Prelogi"
	"\0Premania\0Premedi\0Premusi\0Premythi\0Prepoeti\0Presurgi\0Prevesi"
	"\0Prevo\0Primati\0Prismati\0Probati\0Prochemi\0Procleri\0Proctori\0Produ"
	"\0Proethi\0Prolepti\0Prolifi\0Propheti\0Prosai\0Prosodia\0Prosodi"
	"\0Prosurgi\0Protheti\0Protocer\0Protococ\0Protothe\0Protragi\0Protropi"
	"\0Proven\0Proven\0Psalmodi\0Psychi\0Ptarmi\0Ptolemai\0Pubovesi\0Pudi"
	"\0Pulmoni\0Pulpiti\0Punni\0Puristi\0Puritani\0Pyramidi\0Pyrexi\0Pyriti"
	"\0Pyrologi\0Pythoni\0Quadrati\0Quadrifo\0Quanti\0Quir\0Quixoti\0Quizzi"
	"\0Rabbini\0Radi\0Ramisti\0Ras\0Ras\0Recipro\0Republi\0Retrobuc\0Retrocae"
	"\0Retroce\0Rhapsodi\0Rheologi\0Rhetori\0Rheumati\0Rhinothe\0Rhombi\0Rhon"
	"\0Rhypti\0Rhythmi\0Romanci\0Romanti\0Rubri\0Rumbusti\0Rusti\0Sabbati"
	"\0Sabbati\0Sacrifi\0Salvifi\0Saporifi\0Saraceni\0Sarcasti\0Sardoni\0Sarki"
	"\0Satani\0Satiri\0Satrapi\0Satyri\0Saxoni\0Sceni\0Scepti\0Schemati"
	"\0Sciati\0Scioteri\0Scleroti\0Scopti\0Scorbuti\0Scotisti\0Seismati"
	"\0Seismi\0Seleniti\0Semanti\0Semeioti\0Semicomi\0Semiconi\0Semicubi"
	"\0Semicyni\0Semidomi\0Semiepi\0Semifis\0Semilogi\0Semilyri\0Semimagi"
	"\0Seminifi\0Semioti\0Semiradi\0Semivo\0Semologi\0Sene\0Sensi\0Separati"
	"\0Septi\0Seraphi\0Sermoni\0Serologi\0Sexologi\0Signifi\0Silvi\0Simonia"
	"\0Sini\0Sinologi\0Sinologi\0Sireni\0Skeltoni\0Skepti\0Socrati\0Sodomiti"
	"\0Solomoni\0Somati\0Sophi\0Sophisti\0Soporifi\0Sorboni\0Soriti\0Sothia"
	"\0Souli\0Spagyri\0Spasmati\0Spasmodi\0Specifi\0Spermidu\0Spheri\0Spi"
	"\0Spleneti\0Spleni\0Spondai\0Sporadi\0Stalacti\0Stanzai\0Stati\0Statisti"
	"\0Steri\0Stigmati\0Stoi\0Stomachi\0Strategi\0Stratoni\0Strophi\0Stylisti"
	"\0Stypti\0Subapi\0Subcae\0Subclini\0Subconi\0Subcorti\0Subcriti\0Subcubi"
	"\0Subfo\0Submania\0Subopti\0Subradi\0Subthora\0Subtropi\0Subtypi"
	"\0Subverti\0Subvo\0Suicidi\0Sul\0Superlo\0Suprabuc\0Supracae\0Supralo"
	"\0Surgi\0Sybariti\0Sybariti\0Syllabi\0Syllepti\0Sylvati\0Symbasi"
	"\0Symbioti\0Symboli\0Symmetri\0Symposia\0Symptomi\0Synagogi\0Synapti"
	"\0Synarchi\0Synclini\0Syncreti\0Syndeti\0Syndi\0Synergi\0Synodi\0Synonymi"
	"\0Synopti\0Syntacti\0Syntecti\0Syntheti\0Syntoni\0Syntropi\0Tabifi\0Tacti"
	"\0Talmudi\0Talmudi\0Targumi\0Tas\0Taxonomi\0Techni\0Telergi\0Televo\0Teli"
	"\0Temes\0Tempesti\0Terati\0Terrifi\0Tetani\0Tetrachi\0Tetrathe\0Tetri"
	"\0Thalassi\0Theatri\0The\0Theisti\0Themati\0Theogoni\0Theologi\0Theomagi"
	"\0Theoreti\0Theori\0Theria\0Thermi\0Thermoti\0Thersiti\0Theti\0Theurgi"
	"\0Thomisti\0Thora\0Thoraci\0Thrasoni\0Threneti\0Threnodi\0Thymeli\0Ti"
	"\0Tidologi\0Tin\0Titani\0Tocologi\0Toni\0Tonologi\0Toparchi\0Topheti"
	"\0Topi\0Toplofti\0Topologi\0Toponymi\0Topotypi\0Touristi\0Toxi\0Tragedi"
	"\0Tragi\0Transapi\0Triadi\0Tricksi\0Trifo\0Trifur\0Trilogi\0Trimetri"
	"\0Tripodi\0Triti\0Trocai\0Trophi\0Tropi\0Truisti\0Trun\0Turri\0Twisti"
	"\0Typarchi\0Typi\0Typologi\0Tyranni\0U\0Umbili\0Umbrati\0Unangeli"
	"\0Unbibli\0Unbotani\0Uncanoni\0Uncentri\0Unchemi\0Unclassi\0Uncleri"
	"\0Unclini\0Uncomi\0Unconi\0Uncriti\0Uncubi\0Uncyni\0Undandia\0Undeisti"
	"\0Undomini\0Undropsi\0Undu\0Unempiri\0Unequivo\0Unethi\0Uneugeni"
	"\0Unfanati\0Unfarci\0Unfini\0Unfis\0Ungeneri\0Ungraphi\0Ungui\0Unhereti"
	"\0Unheroi\0Unidenti\0Unifo\0Uninimi\0Uniradi\0Unironi\0Univo\0Unjuridi"
	"\0Unlo\0Unlogi\0Unlyri\0Unmagi\0Unmania\0Unmedi\0Unmetri\0Unmusi\0Unmysti"
	"\0Unmythi\0Unnauti\0Unnover\0Unnumeri\0Unorgani\0Unphysi\0Unpirati"
	"\0Unpoeti\0Unpolemi\0Unpoliti\0Unpracti\0Unprosai\0Unquizzi\0Unradi"
	"\0Unrubri\0Unsatani\0Unsatiri\0Unscepti\0Unskepti\0Unspheri\0Unstati"
	"\0Unstoi\0Unsurgi\0Untacti\0Untechni\0Untragi\0Untropi\0Untypi\0Unveridi"
	"\0Unverti\0Unvo\0Unwhimsi\0Urologi\0Urti\0Uxorilo\0Vari\0Varidi\0Vati"
	"\0Vaticani\0Venati\0Venefi\0Veridi\0Verti\0Vesi\0Vestri\0Vetoisti\0Viati"
	"\0Virilo\0Virologi\0Vivifi\0Vo\0Vorti\0Vulnifi\0Whimsi\0Wrapras\0Wykehami"
	"\0Wykehami\0Xylotomi\0Ya\0Zealoti\0Zodia\0Zoochemi\0Zoologi\0Zoometri"
	"\0Zoonomi\0Zoophysi\0Zoophyti\0Zootomi\0Zymologi";

const char g_prefix_matic[] = "\0Achro\0Ac\0Acous\0Acroa\0Allochro"
	"\0Alloplas\0Allose\0Amphisto\0Anagram\0Analem\0Anallag\0Anastig\0Anathe"
	"\0Aneuris\0Aneurys\0Anidio\0Anos\0Antasth\0Antiasth\0Antidog\0Antienzy"
	"\0Antifog\0Antimias\0Antiprag\0Antirheu\0Antistru\0Aphoris\0Apneu"
	"\0Apochro\0Apophleg\0Apose\0Aposte\0Apoteles\0Apotheg\0Aro\0Aseis\0Asper"
	"\0Astha\0Asth\0Astig\0Asympto\0Asyste\0Athe\0Ato\0Atrau\0Auto\0Autopneu"
	"\0Axio\0Basibreg\0Basichro\0Bichro\0Biocli\0Biosyste\0Bizygo\0Blaste"
	"\0Borboryg\0Brachydo\0Breg\0Cataclys\0Catag\0Categore\0Cau\0Chaino"
	"\0Charis\0Chias\0Chro\0Chromone\0Cine\0Cli\0Clinodo\0Coelo\0Coenzy\0Comag"
	"\0Co\0Com\0Cytostro\0Dal\0Dal\0Der\0Diagram\0Diaphrag\0Diaste\0Diasto"
	"\0Dichro\0Dilem\0Diplo\0Dipris\0Diso\0Dithe\0Dog\0Dra\0Ectoplas\0Emble"
	"\0Empyreu\0Ender\0Engram\0Enig\0Enthyme\0Enzy\0Epider\0Epigram\0Epirrhe"
	"\0Epise\0Erythe\0Euchro\0Exanthe\0Exso\0Extraso\0Foto\0Glosse\0Gram\0Gro"
	"\0Hae\0He\0Hemido\0Hemipris\0Homochro\0Hydroaro\0Hydro\0Hypoder\0Hypomne"
	"\0Hyporche\0Hyposto\0Icono\0Ideogram\0Idiochro\0Idio\0Idioplas\0Is"
	"\0Isochro\0Isocli\0Isoenzy\0Judg\0Keryg\0Kine\0Lepto\0Leptoso\0Lipogram"
	"\0Logogram\0Macrocli\0Macrodo\0Macros\0Mag\0Marem\0Mathe\0Melis\0Melodra"
	"\0Meris\0Meriste\0Mesenchy\0Mesoso\0Metachro\0Metaso\0Mias\0Microcli"
	"\0Micros\0Monochro\0Monodra\0Monogram\0Monoplas\0Monoso\0Monostro\0Ne"
	"\0Neu\0Neurile\0Neurilem\0Nonaro\0Nonasth\0Nonauto\0Nonaxio\0Nonchro"
	"\0Nondiplo\0Nondog\0Nondra\0Nonenig\0Nonhe\0Nonidio\0Nonmathe\0Nonpneu"
	"\0Nonprag\0Nonrheu\0Nonsche\0Nonschis\0Nonsyste\0Nonthe\0Numis\0Ony"
	"\0Orthodo\0Orthoso\0Os\0Osmazo\0Overdog\0Overdra\0Oxychro\0Paleocli"
	"\0Panchro\0Parabe\0Paradig\0Parane\0Parasche\0Parenchy\0Pathe\0Pel"
	"\0Peripleg\0Periso\0Peristo\0Phantas\0Phantas\0Phanto\0Philodra\0Phleg"
	"\0Phone\0Photoder\0Photodra\0Phy\0Pilgri\0Plas\0Pleochro\0Plero\0Pneu"
	"\0Poe\0Polychro\0Polyenzy\0Polygram\0Polyprag\0Polypris\0Polysche\0Polyso"
	"\0Poris\0Postasth\0Postrheu\0Posttrau\0Prag\0Prediplo\0Predra\0Prerheu"
	"\0Presyste\0Pretre\0Prezygo\0Pri\0Pris\0Proble\0Prodra\0Prodro\0Progra"
	"\0Program\0Proso\0Prostem\0Protodra\0Pseudose\0Psychoso\0Rhe\0Rheu\0Rhizo"
	"\0Rick\0Sar\0Sche\0Schis\0Scoto\0Se\0Semiauto\0Semidra\0Semipneu\0Sig"
	"\0Smeg\0Sociodra\0So\0Spas\0Sper\0Staphylo\0Sterig\0Stig\0Sto\0Stratage"
	"\0Stro\0Stru\0Subauto\0Subcli\0Subzygo\0Sympto\0Synallag\0Synapose"
	"\0Synony\0Syste\0Telauto\0Telegram\0Teles\0Teleso\0Ter\0The\0Theore\0Trau"
	"\0Trichro\0Trigram\0Tristig\0Tropis\0Truis\0Unaro\0Unasth\0Unauto\0Unaxio"
	"\0Unchro\0Undiplo\0Undog\0Undra\0Unenig\0Ungram\0Unidio\0Unmias\0Unphleg"
	"\0Unpneu\0Unprag\0Unpris\0Unproble\0Unrheu\0Unsche\0Unschis\0Unsig\0Unso"
	"\0Unstig\0Unsympto\0Unsyste\0Unthe\0Untrau\0Uroso\0Xeroder\0Zeug\0Zoosper"
	"\0Zu\0Zygo";

const char g_prefix_meter[] = "\0Aberro\0Abrasio\0Accelero\0Aceti\0Aceto"
	"\0Acidi\0Acido\0Acou\0Acouo\0Acro\0Actino\0Adapto\0Adhesive\0Adipo\0Aero"
	"\0Aerotono\0Airo\0Albedo\0Albumi\0Albumini\0Albumino\0Alcoholi\0Alcohol"
	"\0Alcoholo\0Alcovino\0Aleuro\0Algesi\0Algesio\0Algo\0Alkali\0Alti\0Alto"
	"\0Ametro\0Am\0Ampere\0Ampero\0Amylo\0Anapno\0Anemo\0Angio\0Angle\0Angulo"
	"\0Anthexi\0Anthraco\0Anthropo\0Anti\0Aperto\0Apomeco\0Apophoro\0Aqua"
	"\0Araeo\0Areo\0Argento\0Arithmo\0Arterio\0Arthro\0Astigmo\0Astro\0Ataxia"
	"\0Atmido\0Atmo\0Audio\0Auxano\0Auxo\0Axo\0Azoto\0Barko\0Baro\0Batho"
	"\0Bathy\0Bdello\0Besiclo\0Bio\0Biophoto\0Blanchi\0Bolo\0Bronto\0Butyro"
	"\0Caelo\0Calci\0Calori\0Campi\0Campylo\0Carboni\0Carbono\0Carburo\0Cardia"
	"\0Cardio\0Catheto\0Ceilo\0Centi\0Cephalo\0Cerebro\0Charto\0Chiro\0Chlori"
	"\0Chloro\0Chromato\0Chromo\0Chronc\0Chrono\0Chyo\0Ci\0Citro\0Climato"
	"\0Clino\0Cliseo\0Coagulo\0Colori\0Comburi\0Compto\0Compto\0Concho"
	"\0Conducti\0Conducto\0Coreo\0Coro\0Coulomb\0Coulo\0Cranio\0Crato\0Creamo"
	"\0Cremo\0Cryo\0Crypto\0Curvi\0Curvo\0Cyano\0Cyclo\0Cyclono\0Cymo\0Cyrto"
	"\0Cysto\0Cyto\0Dasy\0Deca\0Decelero\0Deci\0Declino\0Decolori\0Decre"
	"\0Deflecto\0Defor\0Deka\0De\0De\0Dendro\0Densi\0Densito\0Denti\0Deptho"
	"\0Diabeto\0Diago\0Diagram\0Dia\0Diaphano\0Diasti\0Diffusi\0Diffusio"
	"\0Dilato\0Di\0Diopsi\0Diopto\0Dioptro\0Dip\0Disasti\0Dolori\0Dosi\0Dro"
	"\0Dromo\0Droso\0Drunko\0Ductili\0Duro\0Dyna\0Dynamo\0Ebullio\0Eccentro"
	"\0Echo\0Econo\0Ectropo\0Effusio\0Elaeo\0Elasto\0Elatero\0Elatro\0Electro"
	"\0Eleo\0Ellipso\0Endosmo\0Erg\0Ergo\0Erio\0Esophago\0Esthesio\0Eudio"
	"\0Evapori\0Evaporo\0Exa\0Expanso\0Explosi\0Extensi\0Extenso\0Fadeo\0Farad"
	"\0Farino\0Fatho\0Fatho\0Ferro\0Floodo\0Flow\0Fluidi\0Fluid\0Fluori\0Fluor"
	"\0Fluoro\0Fluvio\0Flux\0Foci\0Foco\0Frigori\0Galacto\0Galvano\0Gaso"
	"\0Gauss\0Gazo\0Geloto\0Geo\0Giga\0Glacio\0Globuli\0Gloss\0Gnatho\0Gonio"
	"\0Gradio\0Grado\0Grapho\0Gravi\0Gravito\0Grum\0Gyro\0Haemato\0Haemo\0Halo"
	"\0Hapto\0Harmono\0Haze\0Hecto\0Hekto\0Helio\0Hemabaro\0Hemacyto\0Hemadro"
	"\0Hemadyna\0Hemati\0Hematino\0Hemato\0Hemocyto\0Hemodro\0Hemodyna"
	"\0Hemomano\0Hemo\0Hepta\0Hexa\0Hippo\0Hodo\0Holo\0Horizo\0Horo\0Hydro"
	"\0Hydroti\0Hyeto\0Hygro\0Hyper\0Hypso\0Hystero\0Icono\0Idio\0Illumino"
	"\0Impedo\0Inclino\0Indigo\0Inducto\0Inspiro\0Isoperi\0Joule\0Karto"
	"\0Katharo\0Kerato\0Kilo\0Kinemo\0Kinesi\0Kinesio\0Koni\0Labido\0Lacto\0La"
	"\0Lana\0Lepto\0Limni\0Limno\0Linea\0Lino\0Litho\0Logo\0Luci\0Lu\0Lumino"
	"\0Lysi\0Mach\0Mach\0Macro\0Magneti\0Magneto\0Mano\0Meato\0Meco\0Mega"
	"\0Megohm\0Meko\0Meldo\0Menti\0Metageo\0Metallo\0Meteoro\0\0\0Methano"
	"\0Metro\0Mho\0Microam\0Microhm\0Micro\0Microno\0Milam\0Mileo\0Milliam"
	"\0Milli\0Milo\0Mino\0Mobilo\0Molari\0Mono\0Multi\0Myria\0Mytho\0Nano"
	"\0Nauropo\0Nephelo\0Nepho\0Nilo\0Nilo\0Nitro\0Occluso\0Octa\0Octo\0Odio"
	"\0Odo\0Odori\0Odoro\0Oeno\0Ohm\0Oilo\0Oleo\0Olfacto\0Ombro\0Omni\0Onco"
	"\0Oncosi\0Onda\0Ondo\0Oo\0Opaci\0Opera\0Opiso\0Opsio\0Opti\0Opto\0Oro"
	"\0Oscillo\0Osmo\0Oxi\0Ozono\0Pacho\0Pachy\0Paedo\0Palato\0Panta\0Panto"
	"\0Para\0Passi\0Passiono\0Passo\0Patho\0Pedo\0Peira\0Pelico\0Pelvi\0Pelyco"
	"\0Penetra\0Penetro\0Penta\0Peri\0Permea\0Phaco\0Pharmaco\0Phase\0Phaseo"
	"\0Phono\0Phoro\0Photo\0Photopto\0Phthongo\0Phyto\0Picno\0Pico\0Piezo"
	"\0Pitcho\0Pitcho\0Pito\0Plani\0Plano\0Plastici\0Plasto\0Platy\0Plego"
	"\0Plemyra\0Plessi\0Plexi\0Plexo\0Pluvio\0Pneomano\0Pneo\0Pneumato\0Pneumo"
	"\0Pneumono\0Podo\0Polari\0Poly\0Poro\0Porosi\0Potamo\0Potentio\0Poto"
	"\0Priso\0Profilo\0Prostato\0Psycho\0Psychro\0Pulmo\0Pulsi\0Pulso\0Pupillo"
	"\0Pursuit\0Pycno\0Pyrano\0Pyrgeo\0Pyrhelio\0Pyro\0Quad\0Quali\0Quanti"
	"\0Quanto\0Rachio\0Radio\0Rate\0Ratio\0Reflecto\0Refracto\0Reo\0Resilio"
	"\0Respiro\0Rheo\0Rhysi\0Rhythmo\0Rota\0Rota\0Roto\0Rougho\0Saccari"
	"\0Sacchari\0Saccharo\0Sali\0Salino\0Salo\0Salto\0Sanguino\0Sclero\0Scolio"
	"\0Secohm\0Seismo\0Semidia\0Semipara\0Semiperi\0Sensito\0Seri\0Shapo"
	"\0Sicci\0Sillo\0Sirio\0Skia\0Sledge\0Slido\0Solari\0Solaro\0Sono\0Spectro"
	"\0Speedo\0Sphero\0Sphingo\0Sphygmo\0Spiro\0Stabili\0Stacto\0Stadi\0Stadio"
	"\0Stagmo\0Stalagmo\0Stato\0Steno\0Stereo\0Stetho\0Strabo\0Straino\0Strata"
	"\0Stylo\0Sub\0Subpara\0Swingo\0Sympieso\0Tacheo\0Tacho\0Tachy\0Tacto"
	"\0Tanno\0Taseo\0Tasi\0Tauto\0Taxa\0Taxi\0Taxo\0Telebaro\0Telemano\0Tele"
	"\0Teleo\0Teles\0Teletopo\0Telluro\0Tendero\0Tensi\0Tensio\0Tenso\0Tenth"
	"\0Tetra\0Thalasso\0Thanato\0Thermoam\0Thermo\0Thoraco\0Tilt\0Tinto"
	"\0Tithono\0Toco\0Tono\0Torsi\0Torsio\0Torso\0Treko\0Tribo\0Trigono\0Tri"
	"\0Trochea\0Trocho\0Tro\0Tromo\0Tropo\0Tropto\0Turbidi\0Turn\0Tyndall\0Udo"
	"\0Urea\0Ureo\0Urethra\0Urethro\0Urino\0Uroacidi\0Uroazoto\0Urogravi\0Uro"
	"\0Utero\0Vacuo\0Vagino\0Vapori\0Vapouri\0Vario\0Veloci\0Velo\0Vento"
	"\0Verti\0Via\0Viato\0Vibro\0Vino\0Visco\0Viscosi\0Visuo\0Volta\0Voltam"
	"\0Volt\0Volumeno\0Volu\0Volumo\0Voto\0Watt\0Wave\0Weighto\0Weighto"
	"\0Xantho\0Xylo\0Yaw\0Zymo\0Zymosi";

const char g_prefix_ferous[] = "\0Acidi\0Actini\0Aeri\0Agati\0Airi"
	"\0Albumini\0Ali\0Alkali\0Alumi\0Alumini\0Aluni\0Amberi\0Amenti\0Ammoniti"
	"\0Amygdali\0Amyli\0Anati\0Anguli\0Antenni\0Antheri\0Anthraci\0Antimoni"
	"\0Aqui\0Arci\0Argenti\0Argilli\0Armi\0Arseni\0Arundi\0Ascidi\0Asci\0Astri"
	"\0Atomi\0Auri\0Axi\0Bacci\0Baculi\0Balani\0Balsami\0Belli\0Bi\0Bili"
	"\0Bismuthi\0Bitumini\0Boraci\0Brachi\0Branchi\0Bulbi\0Byssi\0Cadmi"
	"\0Calami\0Calcari\0Calci\0Calci\0Calyci\0Canali\0Capsuli\0Carboni"
	"\0Carboni\0Carni\0Cauli\0Celli\0Celluli\0Ceri\0Cerumini\0Chaeti\0Chalazi"
	"\0Cheli\0Chromi\0Chyli\0Chymi\0Cili\0Cilii\0Cirri\0Clitelli\0Cobalti"
	"\0Cocci\0Cocculi\0Columbi\0Columni\0Comi\0Conchi\0Conchyli\0Conidii\0Coni"
	"\0Copali\0Coralli\0Corni\0Corni\0Corolli\0Cortici\0Corymbi\0Costi\0Crini"
	"\0Cruci\0Culmi\0Cupri\0Cupuli\0Cymi\0Cysti\0Denti\0Diamanti\0Diamondi"
	"\0Diatomi\0Disci\0Dolori\0Dorsi\0Drupi\0Ef\0Electri\0Elytri\0Embryo"
	"\0Embryoni\0Epidoti\0Esteri\0Fati\0Febri\0\0Ferri\0Feti\0Fibrilli\0Fili"
	"\0Flagelli\0Flammi\0Flori\0Flucti\0Foeti\0Folii\0Folioli\0Foramini"
	"\0Fossili\0Frigi\0Frondi\0Fructi\0Frugi\0Fumi\0Fungi\0Furci\0Galli"
	"\0Garneti\0Gelatini\0Gemmi\0Gemmuli\0Geodi\0Glandi\0Glanduli\0Glauconi"
	"\0Globi\0Globuli\0Glumi\0Gonidi\0Gossani\0Gramini\0Grani\0Graniti"
	"\0Granuli\0Guani\0Gummi\0Gutti\0Gypsi\0Hederi\0Herbi\0Hili\0Hymeni\0Igni"
	"\0Indi\0Indigo\0Infructi\0Insecti\0Iodi\0Isidii\0Jaculi\0Lacti\0Lamelli"
	"\0Lamini\0Lanci\0Lani\0Latici\0Lethi\0Libani\0Ligni\0Ligniti\0Limbi"
	"\0Linguli\0Lipo\0Luci\0Lucri\0Lucti\0Lumini\0Maculi\0Magneti\0Mali"
	"\0Mallei\0Mammali\0Mammi\0Mangani\0Manni\0Maxilli\0Medusi\0Melani\0Melli"
	"\0Membrani\0Menti\0Metalli\0Monstri\0Morbi\0Morti\0Moschi\0Muci\0Mucroni"
	"\0Multi\0Myi\0Nebuli\0Nectari\0Necti\0Niccoli\0Nickeli\0Nimbi\0Nitri"
	"\0Nocti\0Nodi\0Nonauri\0Nonbulbi\0Nonflori\0Nonodori\0Nonproli\0Nubi"
	"\0Nuci\0Nuclei\0Ocelli\0Oculi\0Odi\0Odori\0Olei\0Olivi\0Omni\0Oospori"
	"\0Operculi\0Opsoni\0Osculi\0Ossi\0Ovi\0Ovuli\0Ozoni\0Palladi\0Palmi"
	"\0Palpi\0Paludi\0Papilli\0Pappi\0Papuli\0Paxilli\0Pectini\0Pedi\0Pelti"
	"\0Penni\0Pepsini\0Pesti\0Petali\0Petroli\0Phyti\0Pili\0Pingui\0Pini"
	"\0Pinni\0Pisci\0Pistilli\0Placenti\0Platini\0Plici\0Plumbi\0Polleni"
	"\0Pollini\0Polypi\0Pomi\0Pori\0Potassi\0Proli\0Pruni\0Pulmoni\0Pupi"
	"\0Purpuri\0Pyriti\0Quadrati\0Quartzi\0Racemi\0Radici\0Radi\0Raduli"
	"\0Ramenti\0Rami\0Ramuli\0Rani\0Raphidi\0Reptil\0Resini\0Rori\0Rostri"
	"\0Roti\0Sacchari\0Sacci\0Sagitti\0Sali\0Salini\0Saluti\0Sandi\0Sangui"
	"\0Sanguini\0Saponi\0Sarmenti\0Scopi\0Scopuli\0Scuti\0Scyphi\0Sebi\0Securi"
	"\0Seleni\0Seleniti\0Semi\0Semini\0Seminuli\0Sensi\0Septi\0Serpenti\0Serri"
	"\0Seti\0Silici\0Siliqui\0Siphoni\0Soboli\0Somni\0Soni\0Sonori\0Sopori"
	"\0Soredi\0Sori\0Spermati\0Spici\0Spiculi\0Spini\0Spinuli\0Spiri\0Splendi"
	"\0Spongi\0Sporangi\0Sporidi\0Sporidii\0Spori\0Sporuli\0Spumi\0Squami"
	"\0Stamini\0Stanni\0Stelli\0Stigmati\0Stipuli\0Stoloni\0Stomati\0Strobili"
	"\0Strumi\0Styli\0Suberi\0Succi\0Succini\0Sudori\0Sulphuri\0Tanni\0Tantali"
	"\0Tauri\0Teli\0Telluri\0Tendrili\0Tergi\0Texti\0Thalli\0Thori\0Thuri"
	"\0Thyrisi\0Titani\0Toxi\0Tracti\0Trapi\0Trichini\0Tridenti\0Tri\0Trochi"
	"\0Tuberi\0Tubi\0Tubuli\0Tulipi\0Turioni\0Turri\0Umbelli\0Umbri\0Unceri"
	"\0Unci\0Unguenti\0Ungui\0Unlumini\0Unodori\0Unproli\0Unsopori\0Unvoci"
	"\0Urani\0Urini\0Utriculi\0Vagini\0Valvi\0Vanadi\0Vapori\0Vasculi\0Vasi"
	"\0Veli\0Veneni\0Vermini\0Verruci\0Vesiculi\0Villi\0Vini\0Viruli\0Vitelli"
	"\0Viti\0Voci\0Yttri\0Zinci\0Zinki\0Zirconi\0Zoni\0Zoospori";

const char g_prefix_metric[] = "\0Aceti\0Aceto\0Acidi\0Actino\0Aero"
	"\0Aerotono\0Alcohol\0Alcoholo\0Algo\0Alkali\0Alloio\0Allo\0Ampero\0Anemo"
	"\0Aniso\0Anthraco\0Anthropo\0Antisym\0Areo\0Argento\0Astro\0Asym\0Atmo"
	"\0Audio\0Auto\0Axisym\0Axo\0Axono\0Baro\0Bathy\0Bio\0Biotele\0Bisym\0Bolo"
	"\0Bromo\0Butyro\0Calori\0Cardio\0Catheto\0Cephalo\0Chlori\0Chloro\0Chrono"
	"\0Clino\0Colo\0Colori\0Complexo\0Conducti\0Conducto\0Coulo\0Cranio\0Crato"
	"\0Cyano\0Cyclo\0Cylindro\0Deca\0Densi\0Densito\0Dia\0Diaphano\0Diaphe"
	"\0Dilato\0Di\0Dissym\0Dolori\0Dosi\0Dyna\0Dynamo\0Econo\0Electro\0Endosmo"
	"\0Ergo\0Esthesio\0Eudio\0Fluori\0Fluoro\0Galvano\0Gaso\0Geo\0Gonio"
	"\0Gradio\0Granulo\0Grapho\0Gravi\0Helio\0Hematino\0Hetero\0Hexa\0Hippo"
	"\0Historio\0Holosym\0Hydro\0Hydroti\0Hyeto\0Hygro\0Hypergeo\0Hyper\0Hypso"
	"\0Icono\0Iodi\0Iodo\0Isobaro\0Isodia\0Iso\0Isoperi\0Kerato\0Kilo\0Limni"
	"\0Logo\0Longi\0Lysi\0Magneto\0Mano\0Meso\0\0Micro\0Milli\0Mini\0Monodi"
	"\0Mono\0Monosym\0Morpho\0Nephelo\0Nilo\0Nitro\0Nongeo\0Nonhygro\0Non"
	"\0Nonpara\0Olfacto\0Ombro\0Onco\0Oo\0Opto\0Orobathy\0Oro\0Ortho\0Orthosym"
	"\0Oscillo\0Osmo\0Osteo\0Oxidi\0Oxi\0Pallo\0Panto\0Para\0Pedo\0Pelvi\0Peri"
	"\0Persym\0Phono\0Phoro\0Photo\0Phyto\0Piezo\0Pitheco\0Plani\0Plasto"
	"\0Plessi\0Plexi\0Pluvio\0Polari\0Potentio\0Protogeo\0Pseudo\0Psycho"
	"\0Psychro\0Pyrhelio\0Pyro\0Radio\0Refracto\0Respiro\0Rheo\0Sacchari"
	"\0Saccharo\0Sclero\0Sedi\0Seismo\0Semigeo\0Semisym\0Sensito\0Socio"
	"\0Spectro\0Sphygmo\0Spiro\0Stalagmo\0Stasi\0Stereo\0Stetho\0Sticho"
	"\0Stoichio\0Subgeo\0Sym\0Tacheo\0Tacho\0Tachy\0Tasi\0Tauto\0Tele\0Tensio"
	"\0Thermo\0Tinto\0Titri\0Tono\0Trigono\0Tri\0Tromo\0Turbidi\0Udo\0Undia"
	"\0Ungeo\0Unhygro\0Un\0Unsym\0Urino\0Visco\0Viscosi\0Volta\0Volu\0Zoo";

const char g_prefix_nated[] = "\0Abalie\0Abomi\0Acumi\0Aggluti\0Agmi\0Alie"
	"\0Alter\0Ami\0Assassi\0Benzoi\0Bigemi\0Bilami\0Binomi\0Bipecti\0Bipen"
	"\0Bipin\0Bromi\0Cachin\0Carbo\0Cari\0Cate\0Chlori\0Coadu\0Cognomi\0Colum"
	"\0Commi\0Concacte\0Concate\0Concin\0Congluti\0Conster\0Contami\0Coordi"
	"\0Coro\0Cre\0Crimi\0Cri\0Culmi\0Cyber\0Deami\0Decaffei\0Decarbo\0Decar"
	"\0Dechlori\0Degluti\0Delami\0Delig\0Denomi\0Deoxyge\0Deraci\0Desali"
	"\0Desig\0Determi\0Deto\0Discrimi\0Disordi\0Dissemi\0Domi\0Do\0Ebur\0Echi"
	"\0Effemi\0Elimi\0Ema\0Emargi\0Embryo\0Evagi\0Exsangui\0Extermi\0Fasci"
	"\0Fau\0Ferrugi\0Ferrumi\0Festi\0Fluori\0Forami\0Foreordi\0Fractio\0Fulmi"
	"\0Functio\0Ganglio\0Gelati\0Gemi\0Germi\0Glyceri\0Gobo\0Grati\0Gu"
	"\0Halluci\0Haloge\0Hiber\0Hydroge\0Hyphe\0Illumi\0Imagi\0Impa\0Imperso"
	"\0Impreg\0Incardi\0Incar\0Incoordi\0Incoro\0Incrimi\0Indoctri\0Ingemi"
	"\0Inqui\0Insemi\0Intami\0Intermi\0Into\0Invagi\0Iodi\0Italia\0Lami\0La"
	"\0Lanci\0Lu\0Machi\0Margi\0Mari\0Metha\0Mucro\0Myeli\0Nomi\0Noncarbo"
	"\0Noncre\0Nonincar\0Nonlami\0Nonoxyge\0Nonturbi\0Nonzo\0Nun\0Opinio\0Ordi"
	"\0Origi\0Overdomi\0Oxyge\0Pagi\0Pati\0Pavo\0Pecti\0Pen\0Pepsi\0Peregri"
	"\0Perso\0Pho\0Pin\0Plati\0Polli\0Polylami\0Predesig\0Predesti\0Predomi"
	"\0Predo\0Preelimi\0Prenomi\0Prevacci\0Pro\0Proto\0Pulmo\0Pulvi\0Ratioci"
	"\0Realie\0Recli\0Recrimi\0Redesig\0Redomi\0Reema\0Regermi\0Reillumi"
	"\0Reimpreg\0Reincar\0Rejuve\0Renomi\0Repagi\0Resi\0Reso\0Resupi\0Revacci"
	"\0Rui\0Rumi\0Sacchari\0Sapo\0Semicoro\0Semilu\0Semi\0Semisupi\0Sipho"
	"\0Stag\0Subcari\0Subcre\0Sublu\0Submucro\0Subordi\0Subpecti\0Subunci"
	"\0Sulfo\0Sulpho\0Sulta\0Superan\0Supi\0Termi\0Testudi\0Tricari\0Tripin"
	"\0Turbi\0Umbo\0Unalie\0Unalter\0Uncarbo\0Uncate\0Unchlori\0Unci\0Uncoordi"
	"\0Uncoro\0Undenomi\0Undesig\0Undeto\0Undomi\0Undo\0Uneffemi\0Unelimi"
	"\0Unfasci\0Unfluori\0Unfulmi\0Ungemi\0Ungermi\0Unhyphe\0Unicari\0Unillumi"
	"\0Unimpreg\0Unincar\0Uninvagi\0Unlami\0Unlu\0Unmachi\0Unmargi\0Unmyeli"
	"\0Unnomi\0Unopinio\0Unorigi\0Unoxyge\0Unpagi\0Unpati\0Unpulvi\0Unrejuve"
	"\0Unrui\0Unrumi\0Unsulfo\0Unsulpho\0Untermi\0Unvacci\0Uri\0Vacci\0Vagi"
	"\0Vatici\0Vene\0Verbe\0Vermi\0Zo";

const char g_prefix_stic[] = "\0Absoluti\0Acla\0Acosmi\0Acou\0Acro\0Activi"
	"\0Actuali\0Adiagno\0Aeoli\0Aeroacou\0Aeroela\0Aeropleu\0Agno\0Agoni\0Agre"
	"\0Albini\0Alchemi\0Algori\0Alkahe\0Allegori\0Allopla\0Allothei\0Altrui"
	"\0Amelobla\0Ameri\0Aminopla\0Amne\0Amori\0Amphibla\0Amylocla\0Amylopla"
	"\0Anabapti\0Anacla\0Anacou\0Anacru\0Analogi\0Anamne\0Ananka\0Anapae"
	"\0Anape\0Anapla\0Anarchi\0Anaschi\0Anela\0Anemocla\0Angiobla\0Angiospa"
	"\0Anhi\0Animali\0Anima\0Animati\0Animi\0Annali\0Anomali\0Antagoni"
	"\0Antarchi\0Antibla\0Anticau\0Anticla\0Antidome\0Antidyna\0Antiegoi"
	"\0Antigno\0Antilogi\0Antimy\0Antiorga\0Antipapi\0Antipa\0Antiphra"
	"\0Antipla\0Antispa\0Antithei\0Antonoma\0Aori\0Aphlogi\0Aphori\0Aphrodi"
	"\0Apla\0Apneu\0Apocru\0Apolau\0Apolloni\0Aposiope\0Apriori\0Araphoro"
	"\0Arapho\0Archai\0Archibla\0Ariani\0Arti\0Asbe\0Aschi\0Atavi\0Athei"
	"\0Atmocla\0Atomi\0Atonali\0Auduboni\0Auti\0Autocla\0Autogno\0Autopla"
	"\0Averrhoi\0Averroi\0Avifauni\0Baali\0Balla\0Balli\0Bapti\0Bapti\0Batoni"
	"\0Belletri\0Biblici\0Bigami\0Bima\0Biobla\0Biologi\0Biopla\0Biostati"
	"\0Bolshevi\0Bolshevi\0Bomba\0Borotung\0Bo\0Bovari\0Brahmani\0Browni"
	"\0Bruni\0Buddhi\0Bu\0Cabali\0Cabbali\0Cacoepi\0Cacopla\0Cala\0Calvini"
	"\0Calvini\0Camerali\0Campani\0Canoni\0Capitali\0Careeri\0Carteli\0Casui"
	"\0Catacau\0Catachre\0Catacla\0Catalogi\0Catamne\0Catapla\0Catechi"
	"\0Cathari\0Cau\0Centrali\0Ceropla\0Chala\0Chauvini\0Cheopla\0Chia\0Chilia"
	"\0Chirogno\0Cholecy\0Chori\0Chremati\0Ci\0Cladi\0Classici\0Cla\0Clavieri"
	"\0Coelobla\0Coenobla\0Colori\0Colouri\0Colpopla\0Columni\0Communi"
	"\0Congrui\0Corepla\0Coropla\0Cosmopla\0Cretini\0Cry\0Cubi\0Culti\0Curiali"
	"\0Cycli\0Cy\0Cystospa\0Cytocla\0Cytopla\0Czari\0Dadai\0Dadai\0Daemoni"
	"\0Daimoni\0Darwini\0Darwini\0Dei\0Denti\0Derei\0Deutopla\0Diacau\0Diacla"
	"\0Diagno\0Dialogi\0Diari\0Diaschi\0Dica\0Dicha\0Diplobla\0Discobla"
	"\0Dithei\0Doceti\0Docima\0Dokima\0Dome\0Donati\0Doxa\0Dra\0Duali\0Dueli"
	"\0Duelli\0Duopoli\0Duopsoni\0Dynami\0Dyna\0Dyslogi\0Dysmeri\0Dysphemi"
	"\0Dyspla\0Ecclesia\0Ectobla\0Ectopla\0Ecumeni\0Egoi\0Egoti\0Eki\0Elaeobla"
	"\0Ela\0Elohi\0Emanati\0Empae\0Empai\0Empe\0Empiri\0Empla\0Encau\0Encomia"
	"\0Endobla\0Energeti\0Energi\0Enta\0Enthusia\0Entobla\0Entopla\0Ephelcy"
	"\0Epibla\0Epicera\0Epichori\0Epicla\0Epidei\0Epilogi\0Epina\0Epipa"
	"\0Epispa\0Erethi\0Erga\0Eri\0Erythri\0Esempla\0Essayi\0Eteo\0Euchari"
	"\0Euchari\0Eudemoni\0Eudiagno\0Euhemeri\0Eulogi\0Eumeri\0Euphemi\0Euphui"
	"\0Eupla\0Evangeli\0Exorci\0Extracy\0Extremi\0Factuali\0Famili\0Fanta"
	"\0Fasci\0Fatali\0Fauni\0Federali\0Femini\0Fetichi\0Fetishi\0Feudali"
	"\0Fibrobla\0Fibrocy\0Fibroela\0Fibropla\0Fictioni\0Fidei\0Fi\0Flori"
	"\0Flunkeyi\0Flunkyi\0Folklori\0Formali\0Formuli\0Fourieri\0Fu\0Futuri"
	"\0Gastrocy\0Gela\0Generali\0Genobla\0Geogno\0Germani\0Ge\0Gno\0Gno"
	"\0Gongori\0Gongori\0Gonobla\0Graduali\0Granobla\0Gymna\0Gymnobla\0Haggadi"
	"\0Halaki\0Harmoni\0Hebrai\0Hebrai\0Hedoni\0Hegemoni\0Helia\0Helleni"
	"\0Helleni\0Hemicla\0Hemocla\0Hemopla\0Hemospa\0Henothei\0Hepatocy\0Hephae"
	"\0Heroi\0Hesycha\0Hesycha\0Hetaeri\0Hetairi\0Heuri\0Histocla\0Holi"
	"\0Holobla\0Holocau\0Holocla\0Holophra\0Holopneu\0Homeobla\0Homeopla"
	"\0Homobla\0Homopla\0Hubri\0Hudibra\0Hudibra\0Humani\0Humorali\0Humori"
	"\0Hybri\0Hydrocla\0Hydrocy\0Hygei\0Hygia\0Hylothei\0Hylozoi\0Hypermne"
	"\0Hyperpla\0Hypnoti\0Hypobla\0Hypocori\0Hypona\0Hypopla\0Iconocla\0Ideai"
	"\0Ideali\0Ideopla\0Idiobla\0Idiospa\0Idi\0Idoi\0Idoli\0Idolocla\0Illumini"
	"\0Imagi\0Impla\0Inarti\0Inela\0Infideli\0Intercy\0Interimi\0Inthroni"
	"\0Intracy\0Isacou\0Islami\0Isoela\0Isopie\0Isthmi\0Itaci\0Jahvi\0Jahwi"
	"\0Janseni\0Jargoni\0Jehovi\0Jingoi\0Journali\0Joviali\0Judai\0Judai\0Juri"
	"\0Kar\0Kery\0Klepti\0Labori\0Lamai\0Latini\0Legali\0Legitimi\0Lemmobla"
	"\0Leucobla\0Leukobla\0Liberali\0Lingui\0Lipocla\0Literali\0Lithia"
	"\0Lithocla\0Liturgi\0Locali\0Logi\0Magiri\0Mahayani\0Maje\0Majori\0Mali"
	"\0Mammoni\0Mani\0Manneri\0Manti\0Marini\0Masochi\0Ma\0Ma\0Maximi\0Mechani"
	"\0Mediumi\0Melani\0Meliori\0Melopla\0Mentali\0Meri\0Merobla\0Meroi"
	"\0Mesobla\0Mesopla\0Metagno\0Metaphra\0Metapla\0Metapneu\0Metatung"
	"\0Meteori\0Methodi\0Methodi\0Micracou\0Microcla\0Militari\0Minimi"
	"\0Misogyni\0Misonei\0Misothei\0Mi\0Mithrai\0Mne\0Modali\0Moderni\0Molini"
	"\0Monadi\0Monarchi\0Mona\0Monergi\0Moni\0Monobla\0Monocy\0Monogami"
	"\0Monogeni\0Monopla\0Monopoli\0Monothei\0Montani\0Morali\0Mo\0Muti"
	"\0Mutuali\0Myelobla\0Myelocy\0Myelopla\0Myobla\0Myopla\0Myri\0My\0My"
	"\0Mythocla\0Narcissi\0Narci\0Na\0Nativi\0Naturali\0Naturi\0Navali"
	"\0Negativi\0Nematocy\0Neobla\0Neologi\0Neophra\0Neopla\0Neopla\0Neoteri"
	"\0Nephali\0Nepoti\0Neurobla\0Neuroma\0Neu\0Neutrali\0Nihili\0Nominali"
	"\0Nomi\0Nonacou\0Nonarti\0Nonathei\0Noncasui\0Noncau\0Noncla\0Nondei"
	"\0Nondome\0Nonduali\0Nondyna\0Nonegoi\0Nonegoti\0Nonela\0Nonge\0Nonheuri"
	"\0Nonhubri\0Nonjuri\0Nonlogi\0Nonmona\0Nonmoni\0Nonmy\0Nonpapi\0Nonpla"
	"\0Nonpuri\0Nonreali\0Nonru\0Nonsophi\0Nonstati\0Nonthei\0Normobla\0No"
	"\0Noveli\0Nyctina\0Obligi\0Occami\0Ocellicy\0Oculi\0Oligi\0Oligocy\0Ologi"
	"\0Onani\0Onoma\0Ontologi\0Oobla\0Oocy\0Optimi\0Optoacou\0Orche\0Organici"
	"\0Organi\0Orga\0Orgia\0Origeni\0Ori\0Orleani\0Orthocla\0Orthoepi"
	"\0Orthopla\0Osteobla\0Osteocla\0Osteopla\0O\0Otacou\0Otocy\0Otopla"
	"\0Outstati\0Overcau\0Ovicy\0Ovi\0Pacifici\0Pacifi\0Paedera\0Pagani"
	"\0Paleocry\0Palimpse\0Pancla\0Panlogi\0Panmeri\0Panoi\0Panthei\0Papali"
	"\0Papi\0Parabla\0Paracro\0Paracy\0Paralogi\0Paraphra\0Parapla\0Paratung"
	"\0Pardnoma\0Parodi\0Paronoma\0Partiali\0Pathogno\0Pathopla\0Patri"
	"\0Paulini\0Pedera\0Peira\0Pentacro\0Peribla\0Pericy\0Periphra\0Peripla"
	"\0Peripneu\0Pessimi\0Phanta\0Phenocry\0Phenopla\0Philippi\0Philomy"
	"\0Phlogi\0Photi\0Photoela\0Photona\0Phyllocy\0Physocli\0Piani\0Pieti"
	"\0Pilocy\0Pilpuli\0Pi\0Plagiari\0Planobla\0Pla\0Platoni\0Pleoma\0Pleona"
	"\0Plurali\0Polari\0Polyacou\0Polychre\0Polycy\0Polygami\0Polygeni\0Polyma"
	"\0Polypla\0Polythei\0Polytung\0Popoma\0Populi\0Populi\0Pori\0Pornera"
	"\0Poropla\0Positivi\0Po\0Postorga\0Pragmati\0Prearti\0Precy\0Predome"
	"\0Predyna\0Preformi\0Pregu\0Priori\0Privati\0Proanimi\0Proathei\0Problemi"
	"\0Progno\0Programi\0Propla\0Proreali\0Proti\0Protobla\0Protocla\0Protopla"
	"\0Psittaci\0Pugili\0Puri\0Puseyi\0Pyrocla\0Pyrogno\0Pyrrhoni\0Quieti"
	"\0Rabbini\0Rabuli\0Raciali\0Reali\0Recidivi\0Reformi\0Relativi\0Reunioni"
	"\0Revivali\0Rhapsodi\0Rhinopla\0Rhotaci\0Rigori\0Rigouri\0Rioti\0Rituali"
	"\0Roboti\0Robu\0Romani\0Romani\0Royali\0Ru\0Sadi\0Samsoni\0Sarca"
	"\0Sarcopla\0Satani\0Schedia\0Schi\0Schola\0Schola\0Scholia\0Scienti"
	"\0Scioli\0Scoti\0Seculari\0Semidome\0Semiela\0Semimona\0Semimy\0Seminari"
	"\0Semipla\0Semiru\0Sensi\0Sensuali\0Separati\0Serocy\0Seropla\0Shamani"
	"\0Shintoi\0Shintoi\0Shivai\0Sigili\0Sigilli\0Sila\0Simpli\0Sivai\0Slavi"
	"\0Sociali\0Solari\0Soleci\0Solidari\0Solidi\0Solipsi\0Soloi\0Somatocy"
	"\0Sophi\0Sovieti\0Spa\0Speciali\0Sphragi\0Spinozi\0Spiriti\0Sporocy"
	"\0Stati\0Stocha\0Styli\0Suffragi\0Sufii\0Sufi\0Superela\0Surreali"
	"\0Surreali\0Syllogi\0Symboli\0Symphy\0Symposia\0Syncla\0Syncreti\0Synechi"
	"\0Synerga\0Synergi\0Synopti\0Synopti\0Talmudi\0Tani\0Taoi\0Targumi"
	"\0Telacou\0Telegno\0Telepla\0Tele\0Telobla\0Tenopla\0Termini\0Terrori"
	"\0Thei\0Thelybla\0Theochri\0Theogno\0Theopneu\0Thermona\0Thiotung\0Thomi"
	"\0Timoni\0Toryi\0Totali\0Totemi\0Touri\0Tribadi\0Tribla\0Trichocy"
	"\0Trismegi\0Trithei\0Tropi\0Trui\0Tsari\0Tung\0Tychi\0Tzari\0Ultrai"
	"\0Unacou\0Unaltrui\0Unanimi\0Unarti\0Unauti\0Unbomba\0Uncau\0Undome"
	"\0Unduali\0Unela\0Unfanta\0Unfatali\0Unfuturi\0Ungno\0Ungymna\0Unhedoni"
	"\0Unheuri\0Unhubri\0Unhumani\0Unideali\0Unigeni\0Unioni\0Uniti\0Unlogi"
	"\0Unmaje\0Unmona\0Unmoni\0Unmorali\0Unmy\0Unnihili\0Unoptimi\0Unpacifi"
	"\0Unpatri\0Unpla\0Unpugili\0Unpuri\0Unreali\0Unru\0Unsadi\0Unsarca"
	"\0Unschola\0Unsophi\0Unstati\0Unthei\0Uranopla\0Urbani\0Urocy\0Utopi"
	"\0Utraqui\0Vagari\0Vandali\0Vasospa\0Verbali\0Veri\0Veriti\0Vetoi"
	"\0Violini\0Viscoela\0Vitali\0Vocali\0Voodooi\0Voyeuri\0Welfari\0Wholi"
	"\0Xenocry\0Xenopla\0Xylopla\0Yahvi\0Yahwi\0Yahwi\0Zioni\0Zoi\0Zolai"
	"\0Zoocy\0Zoopla\0Zoothei\0Zymopla";

const char g_prefix_opic[] = "\0Ac\0Acrosc\0Adenect\0Adrenotr\0Aeolotr"
	"\0Aerosc\0Aerotr\0Aes\0Aetiotr\0Aitiotr\0Allelotr\0Allotr\0Ambly\0Ametr"
	"\0Anemotr\0Anisotr\0Anthotr\0Anthr\0Antihydr\0Antimetr\0Antitr\0Aphototr"
	"\0Apoc\0Apogeotr\0Arthrotr\0Asthen\0At\0Atr\0Aurisc\0Autosc\0Autotr"
	"\0Azeotr\0Barosc\0Barotr\0Basisc\0Bathmotr\0Bi\0Biosc\0Bo\0Bothr\0Can"
	"\0Can\0Chemiotr\0Chemotr\0Chromosc\0Chromotr\0Chronosc\0Chronotr"
	"\0Chrysatr\0CinemaSc\0Conosc\0Cryosc\0Cycl\0Cycl\0Cystosc\0Cytotr"
	"\0Dermatr\0Dermotr\0Desmotr\0Deuteran\0Dexiotr\0Dextrotr\0Diageotr\0Diatr"
	"\0Dichrosc\0Dipl\0Dromotr\0Ecot\0Ect\0Ectotr\0Embrosc\0Embryosc\0Emmetr"
	"\0Endosc\0Endotr\0Ent\0Entr\0Eolotr\0Epidiasc\0Esotr\0Ethi\0Ethi\0Etiotr"
	"\0Eurypros\0Euryt\0Eurytr\0Euthytr\0Eutr\0Exotr\0Fluorosc\0Gamotr"
	"\0Gastrosc\0Geosc\0Geotr\0Gonadotr\0Gyrosc\0Hagiosc\0Haplosc\0Haptotr"
	"\0Heliosc\0Heliotr\0Hemeral\0Hemian\0Hemi\0Hemitr\0Hemotr\0Heterot"
	"\0Heterotr\0Histotr\0Homot\0Horosc\0Hydratr\0Hydr\0Hydrosc\0Hydrotr"
	"\0Hygrosc\0Hylotr\0Hyper\0Idiotr\0Inotr\0Intertr\0Isentr\0Isorr\0Isot"
	"\0Isotr\0Kinetosc\0Laeotr\0Lecanosc\0Leiotr\0Lipotr\0Luteotr\0Lycanthr"
	"\0Lychnosc\0Lyotr\0Macrosc\0Magnasc\0Megal\0Megasc\0Mer\0Mes\0Mesopros"
	"\0Mesotr\0Met\0Metoposc\0Metrect\0Microsc\0Misanthr\0Monotr\0Morphotr"
	"\0Mutosc\0My\0Neanthr\0Necrosc\0Neoanthr\0Neotr\0Neurotr\0Nonisotr\0Nonmy"
	"\0Nontr\0Noosc\0Nyctal\0Nyctitr\0Oligotr\0Oneirosc\0Organotr\0Ornisc"
	"\0Orthomet\0Orthosc\0Orthotr\0Otosc\0Ozonosc\0Palin\0Pantasc\0Pantosc"
	"\0Pantr\0Peric\0Perisc\0Phot\0Photosc\0Phototr\0Phrenotr\0Plagiotr"
	"\0Planisc\0Plat\0Platy\0Pleiotr\0Pluviosc\0Pneumotr\0Polarisc\0Polyisot"
	"\0Poly\0Polysc\0Polyt\0Polytr\0Porosc\0Presby\0Proctosc\0Progeotr\0Pros"
	"\0Protan\0Pseudosc\0Psychotr\0Radiosc\0Radiotr\0Retinosc\0Rheosc\0Rheotr"
	"\0Rhinosc\0Sc\0Scot\0Seismosc\0Selenotr\0Semitr\0Sin\0Sin\0Somatotr"
	"\0Staurosc\0Stenot\0Stenotr\0Stereosc\0Stereotr\0Stethosc\0Strobosc\0Subt"
	"\0Subtr\0Sync\0Syntr\0Telesc\0Thaumosc\0Theanthr\0Thermosc\0Thermotr"
	"\0Thigmotr\0Thixotr\0Thyreotr\0Thyrotr\0T\0Traumatr\0Tritan\0Trophotr\0Tr"
	"\0Unhorosc\0Unisotr\0Unmy\0Untr\0Uranosc\0Urinosc\0Urosc\0Vagotr\0Vibrosc"
	"\0Vitasc\0Xenotr\0Zoetr\0Zoosc";

const char g_prefix_ected[] = "\0Adf\0Adv\0Aff\0Antefl\0Biconn\0Bifl\0Bis"
	"\0Cath\0Codir\0Coer\0Coll\0Compl\0Conf\0Conn\0Conv\0Corr\0Def\0Defl\0Dej"
	"\0Desel\0Det\0Dir\0Disaff\0Disconn\0Disinf\0Disj\0Diss\0Eff\0Ej\0El\0Er"
	"\0Ev\0Exp\0Exs\0Genufl\0Imperf\0Inaff\0Inconn\0Indir\0Inexp\0Inf\0Infl"
	"\0Inj\0Ins\0Insp\0Intell\0Interj\0Inters\0Introsp\0Inv\0Misaff\0Miscorr"
	"\0Misdir\0Miser\0Negl\0Nondefl\0Nonel\0Noninf\0Noninfl\0Nonperf\0Nonrefl"
	"\0Nonsel\0Nonsubj\0Obj\0Obt\0Overaff\0Overcorr\0Overprot\0Palmatis"
	"\0Pedatis\0Pennatis\0Perf\0Pinnatis\0Pinnis\0Prael\0Predil\0Preel\0Prel"
	"\0Presel\0Proj\0Pros\0Prosp\0Prot\0Quadris\0Recoll\0Reconn\0Redir\0Reej"
	"\0Reel\0Reer\0Ref\0Refl\0Reinf\0Reinsp\0Rej\0Reobj\0Res\0Resel\0Resp"
	"\0Resurr\0Retrofl\0Sel\0Semiprot\0Subj\0Susp\0Traj\0Trans\0Tris\0Unaff"
	"\0Unarchit\0Uncoll\0Unconf\0Unconn\0Uncorr\0Undefl\0Undej\0Undet\0Undir"
	"\0Undisinf\0Undiss\0Uneff\0Unej\0Unel\0Uner\0Unexp\0Unidir\0Uninf\0Uninfl"
	"\0Uninj\0Uninsp\0Uninterj\0Uninters\0Unnegl\0Unobj\0Unperf\0Unproj"
	"\0Unprosp\0Unprot\0Unrecoll\0Unrefl\0Unrej\0Unresp\0Unresurr\0Unsel"
	"\0Unsubj\0Unsusp\0Vivis\0Wellaff\0Wellconn";

const char g_prefix_graph[] = "\0Accelero\0Actino\0Addresso\0Aero\0Air"
	"\0Albedo\0Allo\0Alti\0Ana\0Anapno\0Anemobia\0Anemo\0Aneroido\0Angio"
	"\0Animato\0Anti\0Apo\0Arco\0Arithmo\0Arterio\0Astro\0Ataxia\0Atmo"
	"\0Autoepi\0Auto\0Automato\0Autotele\0Auxo\0Baro\0Biblio\0Bio\0Bolo"
	"\0Bronto\0Calcula\0Calli\0Cameo\0Cardia\0Cardio\0Carto\0Cathode\0Cathodo"
	"\0Catho\0Ceco\0Cephalo\0Cerauno\0Cero\0Chalco\0Chemi\0China\0Chiro"
	"\0Choreo\0Choro\0Chromato\0Chromo\0Chrono\0Chryso\0Cinemato\0Cinemo"
	"\0Climo\0Clino\0Comparo\0Composo\0Copy\0Corona\0Corono\0Cranio\0Cresco"
	"\0Crypto\0Crysto\0Curvo\0Cyclo\0Cylindro\0Cyma\0Cymo\0Cyrto\0Dactylo"
	"\0Declino\0Decrypto\0Demono\0Dendro\0Dermato\0Dia\0Dicta\0Dicto\0Dicto"
	"\0Di\0Diopto\0Diplo\0Ditto\0Dromo\0Droso\0Duo\0Dyna\0Dynamo\0Echo\0Eido"
	"\0Electro\0Ellipso\0Ellipto\0Entero\0Epi\0Ergo\0Exo\0Fluvio\0Flux"
	"\0Galvano\0Gastro\0Glosso\0Glypho\0Glypto\0\0Gyro\0Harmono\0Hecto\0Hekto"
	"\0Helico\0Helio\0Hemauto\0Hiero\0Historio\0Hodo\0Holo\0Homo\0Horo\0Hurry"
	"\0Hyalo\0Hydro\0Hyeto\0Hygro\0Hypno\0Hyther\0Icono\0Ideo\0Idio\0Inclino"
	"\0Inte\0Iso\0Isometro\0Kerauno\0Kinemato\0Kineto\0Klydono\0Kymo\0Labio"
	"\0Laryngo\0Limno\0Lineo\0Litho\0Logo\0Loxodo\0Macro\0Magneto\0Mano"
	"\0Marconi\0Mareo\0Mari\0Megalo\0Melodio\0Melo\0Metallo\0Meteo\0Meteor"
	"\0Meteoro\0Mezzo\0Micro\0Mimeo\0Mimeo\0Mono\0Moto\0Multi\0Multi\0Myo"
	"\0Nepho\0Nocto\0Nomo\0Odo\0Odonto\0Oleo\0Olo\0Ombro\0Omni\0Onco\0Onda"
	"\0Ondo\0Oo\0Opistho\0Opti\0Oro\0Orohelio\0Orthodia\0Ortho\0Oscillo\0Osmo"
	"\0Palaeo\0Palato\0Paleo\0Pallo\0Panicono\0Panta\0Pantele\0Panto\0Papyro"
	"\0Para\0Pedo\0Pelvi\0Perfilo\0Peri\0Periodo\0Petro\0Pezo\0Philo\0Phlebo"
	"\0Phonauto\0Phono\0Photo\0Phraseo\0Phreno\0Phyto\0Piano\0Picto\0Pistol"
	"\0Plagio\0Plani\0Plano\0Plessi\0Pluvio\0Pneo\0Pneumato\0Pneumo\0Polaro"
	"\0Polaro\0Poly\0Pono\0Porno\0Pretele\0Profilo\0Protecto\0Proto\0Psalmo"
	"\0Pseudepi\0Pseudo\0Psycho\0Psychro\0Pyelo\0Pyro\0Rachi\0Radio\0Recti\0Re"
	"\0Repara\0Rephoto\0Retele\0Roto\0Scatter\0Sceno\0Schemato\0Scia\0Scio"
	"\0Scoto\0Sculpto\0Seismo\0Seleno\0Seri\0Shadow\0Sillo\0Skia\0Skio"
	"\0Spectro\0Sphero\0Sphygmo\0Spiro\0Steno\0Stereo\0Stetho\0Steven\0Stomato"
	"\0Stylo\0Sub\0Subpara\0Sympalmo\0Syn\0Tacho\0Tachy\0TelAuto\0Telauto"
	"\0Telauto\0Telebaro\0Telectro\0Tele\0Telli\0Theatro\0Thermeto\0Thermo"
	"\0Thoraco\0Tomo\0Tono\0Topo\0Torsi\0Torsio\0Traina\0Tri\0Trypo\0Typo"
	"\0Typotele\0Udomo\0Uretero\0Urethra\0Urethro\0Vaporo\0Vecto\0Via\0Vibro"
	"\0Visa\0Vita\0Voto\0Xo\0Xylo\0Zinco";

const char g_prefix_scope[] = "\0Abdomino\0Aberro\0Aerobio\0Aero\0Aethrio"
	"\0Albumino\0Albumo\0Aletho\0Aleuro\0Alti\0Amblyo\0Anemo\0Angio\0Anomalo"
	"\0Anortho\0Ano\0Anoxy\0Antro\0Aphenge\0Aphengo\0Apheno\0Aqua\0Arero"
	"\0Astigmo\0Astro\0Auri\0Ausculta\0Ausculto\0Ausculto\0Autecho\0Auto\0Baro"
	"\0Bentho\0Biomicro\0Bio\0Broncho\0Cardio\0Cava\0Celio\0Celo\0Cerauno"
	"\0Cerebro\0Chorepi\0Chroma\0Chromato\0Chromo\0Chrono\0Cinema\0Cinema"
	"\0Coelo\0Colono\0Colpo\0Compara\0Cono\0Cosmo\0Cryo\0Crypto\0Cyclono"
	"\0Cyclo\0Cymo\0Cysto\0Defecto\0Devia\0Diaphano\0Dia\0Dichroi\0Dichroo"
	"\0Dichro\0Dipleido\0Dynamo\0Ebullio\0Electro\0Embryo\0Endo\0Engi\0Engy"
	"\0Entero\0Entopto\0Epidia\0Epi\0Erythro\0Esophago\0Eury\0Fiber\0Flori"
	"\0Floro\0Fluoro\0Galacto\0Galvano\0Gaso\0Gastro\0Glotti\0Grapho\0Gyro"
	"\0Hagio\0Halo\0Haplo\0Helio\0Hemato\0Hemo\0Hetero\0Hodo\0Holo\0Horo"
	"\0Hydro\0Hygro\0Hypo\0Hystero\0Icono\0Icono\0Inducto\0Intro\0Iri\0Iso"
	"\0Isoteni\0Kaleide\0Kaleido\0Kerato\0Kine\0Kineto\0Koni\0Lacto\0Laparo"
	"\0Laryngo\0Litho\0Lychno\0Magna\0Magneto\0Mano\0Meato\0Megalo\0Mega"
	"\0Melano\0Metalo\0Meta\0Meteoro\0Meteor\0Metro\0Micro\0Mirror\0Mono\0Muto"
	"\0Myo\0Myrio\0Naso\0Nephelo\0Nepho\0Nilo\0Odonto\0Omni\0Onda\0Ondo\0Oo"
	"\0Opeido\0Ortho\0Oscillo\0Osmo\0Osteo\0Otheo\0Oto\0Ozono\0Pago\0Panta"
	"\0Panto\0Periodo\0Peri\0Phacoido\0Phaco\0Phanero\0Phanta\0Phanto"
	"\0Pharyngo\0Phoneido\0Phonele\0Phonendo\0Phono\0Phoro\0Photo\0Pio\0Plani"
	"\0Pluvio\0Pneo\0Pneumato\0Polari\0Polemo\0Poly\0Poro\0Praxino\0Procto"
	"\0Pseudo\0Pupillo\0Pyro\0Radar\0Radio\0Recto\0Reflecto\0Resecto\0Retino"
	"\0Rheo\0Rhino\0Rifle\0Rontgeno\0Rota\0Saccharo\0Salpingo\0Schisto\0Scia"
	"\0Sclero\0Sclero\0\0Scoto\0Seismo\0Seleno\0Sidero\0Sigmoido\0Skia\0Sniper"
	"\0Snooper\0Spectro\0Sphygmo\0Spiro\0Stati\0Stato\0Stauro\0Stereo\0Stetho"
	"\0Stomato\0Strobo\0Synchro\0Tachisto\0Tacho\0Tachy\0Teino\0Telectro"
	"\0Telengi\0Tele\0Theatro\0Thermo\0Thoraco\0Thora\0Tono\0Trichino\0Urano"
	"\0Urethra\0Urethro\0Utero\0Vagino\0Vera\0Veri\0Vibro\0Visco\0Vita\0Volume"
	"\0Zeo\0Zoopraxi\0Zymo";

#endif/*__DB_H__*/
