meriac/openbeacon-ng/firmware/nRF51/tag-mischief/src/radio.c

/***************************************************************
 *
 * OpenBeacon.org - nRF51 2.4GHz Radio Routines
 *
 * Copyright 2013 Milosch Meriac <meriac@openbeacon.de>
 *
 ***************************************************************

 This file is part of the OpenBeacon.org active RFID firmware

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
*/
#include <openbeacon.h>
#include <main.h>
#include <radio.h>
#include <adc.h>
#include <timer.h>
#include <name.h>

/* don't start DC/DC converter for voltages below 2.3V */
#define NRF_DCDC_STARTUP_VOLTAGE 23

#define BLE_ADDRESS 0x8E89BED6UL
#define BLE_PREFIX_SIZE 9
#define BLE_POSTFIX (BLE_PREFIX_SIZE+2)

#define TAG_COUNT 23

typedef struct {
	uint8_t channel;
	uint8_t frequency;
} TMapping;

static volatile int g_advertisment_index;
static volatile uint32_t g_iteration;
volatile uint32_t  g_counter;

static uint32_t g_uid;
static uint8_t g_pkt_buffer[64];

static const TMapping g_advertisment[] = {
	{37,  2},
	{38, 26},
	{39, 80},
};
#define ADVERTISMENT_CHANNELS ((int)(sizeof(g_advertisment)/sizeof(g_advertisment[0])))

void RTC0_IRQ_Handler(void)
{
	/* run five times per second */
	if(NRF_RTC0->EVENTS_COMPARE[0])
	{
		/* acknowledge event */
		NRF_RTC0->EVENTS_COMPARE[0] = 0;

		/* re-trigger timer */
		NRF_RTC0->CC[0] = NRF_RTC0->COUNTER + MILLISECONDS(200);

		/* start HF crystal oscillator */
		NRF_CLOCK->TASKS_HFCLKSTART = 1;

		/* start ADC conversion */
		adc_start();

		/* only start DC/DC converter for
		 * RX & higher battery voltages */
		if(adc_bat()>=NRF_DCDC_STARTUP_VOLTAGE)
		{
			/* start DC-DC converter */
			NRF_POWER->DCDCEN = (
				(POWER_DCDCEN_DCDCEN_Enabled << POWER_DCDCEN_DCDCEN_Pos)
			);
		}
	}
}

static void radio_send_advertisment_repeat(void)
{
	const TMapping *map;

	/* transmit beacon on all advertisment channels */
	map = &g_advertisment[g_advertisment_index];

	/* switch frequency & whitening */
	NRF_RADIO->FREQUENCY = map->frequency;
	NRF_RADIO->DATAWHITEIV = map->channel;

	/* set packet pointer */
	NRF_RADIO->PACKETPTR = (uint32_t)&g_pkt_buffer;

	/* start tracker TX */
	NRF_RADIO->EVENTS_END = 0;
	NRF_RADIO->TASKS_TXEN = 1;
}

static void radio_send_advertisment(void)
{
	uint8_t pos;
	uint32_t counter, seed1, seed2;

	counter = g_iteration + g_counter;
	seed1 = crc32(&counter, sizeof(counter));
	seed2 = crc32(&seed1, sizeof(seed1));

	/* BLE header */
	g_pkt_buffer[0] = 0x42;

	/* add MAC address */
	memcpy(&g_pkt_buffer[2], &seed1, 4);
	memcpy(&g_pkt_buffer[6], &seed2, 2);

	/* No BT/EDR - Tx only */
	g_pkt_buffer[8] = 2;
	g_pkt_buffer[9] = 0x01;
	g_pkt_buffer[10]= 0x04;

	/* append name */
	pos = name( 25, (char*)&g_pkt_buffer[BLE_POSTFIX+2], seed1 );

	/* calculate total packet size */
	g_pkt_buffer[1] = BLE_POSTFIX + pos;

	g_pkt_buffer[BLE_POSTFIX]   = pos+1;
	g_pkt_buffer[BLE_POSTFIX+1] = 0x08;

//	hex_dump(g_pkt_buffer, 0, g_pkt_buffer[1]+2);

	/* send first packet */
	g_advertisment_index = 0;
	radio_send_advertisment_repeat();
}

void POWER_CLOCK_IRQ_Handler(void)
{
	/* always transmit proximity packet */
	if(NRF_CLOCK->EVENTS_HFCLKSTARTED)
	{
		/* acknowledge event */
		NRF_CLOCK->EVENTS_HFCLKSTARTED = 0;

		/* send first packet */
		radio_send_advertisment();
	}
}

void RADIO_IRQ_Handler(void)
{
	/* transmitted packet */
	if(NRF_RADIO->EVENTS_DISABLED)
	{
		/* acknowledge event */
		NRF_RADIO->EVENTS_DISABLED = 0;

		/* switch to next channel */
		g_advertisment_index++;
		if(g_advertisment_index<ADVERTISMENT_CHANNELS)
			radio_send_advertisment_repeat();
		else
		{
			g_advertisment_index = 0;

			/* progress to next packet:
			 * ensure that every packet is transmitted
			 * g_iteration times */
			if(g_iteration<TAG_COUNT)
			{
				g_iteration++;

				radio_send_advertisment();
			}
			else
			{
				g_iteration = 0;

				/* stop HF clock */
				NRF_CLOCK->TASKS_HFCLKSTOP = 1;
				/* disable DC-DC converter */
				NRF_POWER->DCDCEN = 0;
			}
		}
	}

	/* acknowledge event */
	if(NRF_RADIO->EVENTS_END)
		NRF_RADIO->EVENTS_END = 0;
}

void radio_init(uint32_t uid)
{
	/* remember uid */
	g_uid = g_counter = uid;

	/* reset sequence counter */
	g_iteration = 0;

	/* initialize ADC battery voltage measurements */
	adc_init();

	/* setup default radio settings for proximity mode */
	NRF_RADIO->MODE = RADIO_MODE_MODE_Ble_1Mbit << RADIO_MODE_MODE_Pos;
	NRF_RADIO->TXPOWER = RADIO_TXPOWER_TXPOWER_Pos4dBm;
	NRF_RADIO->TXADDRESS = 0;
	NRF_RADIO->PREFIX0 = ((BLE_ADDRESS>>24) & RADIO_PREFIX0_AP0_Msk);
	NRF_RADIO->BASE0 = (BLE_ADDRESS<<8);
	NRF_RADIO->RXADDRESSES = 0;
	NRF_RADIO->PCNF0 =
		(1 << RADIO_PCNF0_S0LEN_Pos)|
		(8 << RADIO_PCNF0_LFLEN_Pos);
	NRF_RADIO->PCNF1 =
		(RADIO_PCNF1_WHITEEN_Enabled << RADIO_PCNF1_WHITEEN_Pos)|
		(0xFF                        << RADIO_PCNF1_MAXLEN_Pos)|
		(3 << RADIO_PCNF1_BALEN_Pos);
	NRF_RADIO->CRCCNF =
		(RADIO_CRCCNF_LEN_Three << RADIO_CRCCNF_LEN_Pos) |
		(1 << RADIO_CRCCNF_SKIP_ADDR_Pos);
	NRF_RADIO->CRCINIT = 0x00555555UL;
	NRF_RADIO->CRCPOLY = 0x0100065BUL;
	NRF_RADIO->SHORTS = (
		(RADIO_SHORTS_READY_START_Enabled       << RADIO_SHORTS_READY_START_Pos) |
		(RADIO_SHORTS_END_DISABLE_Enabled       << RADIO_SHORTS_END_DISABLE_Pos)
	);
	NRF_RADIO->INTENSET = (
		(RADIO_INTENSET_DISABLED_Enabled        << RADIO_INTENSET_DISABLED_Pos) |
		(RADIO_INTENSET_END_Enabled             << RADIO_INTENSET_END_Pos)
	);
	NVIC_SetPriority(RADIO_IRQn, IRQ_PRIORITY_RADIO);
	NVIC_EnableIRQ(RADIO_IRQn);

	/* setup HF-clock IRQ */
	NRF_CLOCK->INTENSET = (
		(CLOCK_INTENSET_HFCLKSTARTED_Enabled << CLOCK_INTENSET_HFCLKSTARTED_Pos)
	);
	NVIC_SetPriority(POWER_CLOCK_IRQn, IRQ_PRIORITY_POWER_CLOCK);
	NVIC_EnableIRQ(POWER_CLOCK_IRQn);

	/* setup radio timer */
	NRF_RTC0->TASKS_STOP = 1;
	NRF_RTC0->COUNTER = 0;
	NRF_RTC0->PRESCALER = 0;
	NRF_RTC0->CC[0] = LF_FREQUENCY;
	NRF_RTC0->INTENSET = (
		(RTC_INTENSET_COMPARE0_Enabled   << RTC_INTENSET_COMPARE0_Pos)
	);
	NVIC_SetPriority(RTC0_IRQn, IRQ_PRIORITY_RTC0);
	NVIC_EnableIRQ(RTC0_IRQn);
	NRF_RTC0->TASKS_START = 1;
}
