meriac/openbeacon-ng/host/openbeacon-sniffer/openbeacon-proto.h

/****************************************************************************
 *
 * OpenBeacon.org - OnAir protocol specification and definition
 *
 * Copyright 2013 Milosch Meriac <meriac@openbeacon.de>
 *
 ****************************************************************************

 This file is part of the OpenBeacon.org active RFID firmware

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
*/

#ifndef __OPENBEACON_PROTO_H__
#define __OPENBEACON_PROTO_H__

#define BEACONLOG_SIGHTING 0x01

#define CONFIG_TRACKER_CHANNEL 81
#define CONFIG_PROX_CHANNEL 76

#define CONFIG_SIGNATURE_SIZE 5
#define CONFIG_SIGHTING_SLOTS 3

#define RFBPROTO_BEACON_NG_SIGHTING 30
#define RFBPROTO_BEACON_NG_STATUS   31
#define RFBPROTO_BEACON_NG_PROX     32
#define RFBPROTO_PROTO_MASK       0x7F
#define RFBPROTO_PROTO_BUTTON     0x80

#define PROXSIGHTING_PAGE_FORMAT_FIRST 0x01
#define PROXSIGHTING_PAGE_FORMAT_NEXT 0x02


#define MARKER_TAG_BIT (1UL<<31)

typedef struct
{
	int16_t rx_loss;
	int16_t tx_loss;
	int16_t px_power;
	uint16_t ticks;
} PACKED TBeaconNgStatus;

typedef struct
{
	int8_t rx_power;
	uint32_t uid;
} PACKED TBeaconNgSighting;

typedef union
{
	TBeaconNgStatus status;
	TBeaconNgSighting sighting[CONFIG_SIGHTING_SLOTS];
	uint8_t raw[15];
} PACKED TBeaconNgPayload;

typedef struct
{
	uint8_t proto;
	int8_t tx_power;
	int8_t angle;
	uint8_t voltage;
	uint32_t uid;
	uint32_t epoch;
	TBeaconNgPayload p;
 	uint8_t signature[CONFIG_SIGNATURE_SIZE];
} PACKED TBeaconNgTracker;

typedef struct
{
	uint32_t uid;
	uint32_t epoch;
	uint16_t ticks;
} PACKED TBeaconNgProxAnnounce;

typedef union
{
	TBeaconNgProxAnnounce prox;
	uint8_t raw[10];
} PACKED TBeaconNgProxPayload;

typedef struct
{
	TBeaconNgProxPayload p;
	uint8_t proto;
	uint8_t signature[CONFIG_SIGNATURE_SIZE];
} PACKED TBeaconNgProx;

typedef struct
{
	uint16_t icrc16;
	uint8_t protocol;
	uint8_t interface;
	uint16_t reader_id;
	uint16_t size;
} PACKED TBeaconNetworkHdr;

/* BEACONLOG_SIGHTING */
typedef struct
{
	TBeaconNetworkHdr hdr;
	uint32_t sequence;
	uint32_t timestamp;
	TBeaconNgTracker log;
} PACKED TBeaconLogSighting;

typedef struct
{
	uint32_t tag_id;
	uint32_t epoch_local, epoch_remote;
	int8_t power;
	int8_t angle;
} PACKED TBeaconProxSighting;

#define BEACON_PROXSIGHTING_PAGE_MARKER 0x8000U
#define BEACON_PROXSIGHTING_LENGTH_MASK 0x0FFFU
typedef struct
{
	uint16_t length;
	uint8_t buffer[258];
	uint32_t crc32;
} PACKED TBeaconProxSightingPage;

#endif/*__OPENBEACON_PROTO_H__*/
