meriac/openbeacon-ng/host/openbeacon-power/src/bmMapHandleToItem.cpp

/***************************************************************
 *
 * OpenBeacon.org - OnAir protocol position estimator
 * accepts a text file with tag sightings per reader.
 *
 * See the following website for already decoded Sputnik data:
 * http://people.openpcd.org/meri/openbeacon/sputnik/data/24c3/
 *
 * Copyright 2009 Milosch Meriac <meriac@bitmanufaktur.de>
 *
 ***************************************************************/

/*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
 You should have received a copy of the GNU Affero General Public License
 along with this program; if not, write to the Free Software Foundation,
 Inc., 51 Franklin Street, Fifth Floor, Boston, MA 02110-1301 USA.
 */

#include <stdio.h>
#include <stdlib.h>
#include <string.h>
#include <stdint.h>
#include <pthread.h>

#include "bmMapHandleToItem.h"
#include "crc32.h"

bmMapHandleToItem::bmMapHandleToItem (void)
{
	m_ItemSize = m_MapIteratePos = 0;
	memset (&m_Map, 0, sizeof (m_Map));
	memset (&m_MapIterate, 0, sizeof (m_MapIterate));
}

bmMapHandleToItem::~bmMapHandleToItem (void)
{
	int i;
	bmHandleMap *map = m_Map;

	if (m_ItemSize > (int) sizeof (map->data))
		for (i = 0; i < HASH_MAP_INDEX_SIZE; i++)
		{
			if (map->handle)
				free (map->data);
			map++;
		}
}

bool bmMapHandleToItem::SetItemSize (int ItemSize)
{
	if (ItemSize <= 0 || m_ItemSize)
		return false;
	else
	{
		m_ItemSize = ItemSize;
		return true;
	}
}

int
bmMapHandleToItem::GetItemSize (void)
{
	return m_ItemSize;
}

bmHandleMap *
bmMapHandleToItem::HashMap (bmHandle handle)
{
	int i;
	uint32_t crc32 = 0xffffffffL;

	for (i = 0; i < (int) sizeof (handle); i++)
	{
		crc32 =
			crc32_table[(uint8_t) crc32 ^ (uint8_t) handle] ^ (crc32 >> 8);
		handle >>= 8;
	}

	return &m_Map[(crc32 ^ 0xffffffffUL) % HASH_MAP_INDEX_SIZE];
}

void *
bmMapHandleToItem::Find (bmHandle handle, pthread_mutex_t ** mutex)
{
	bmHandleMap *map;
	int i;

	if (m_ItemSize && handle)
	{

		map = HashMap (handle);

		for (i = 0; i < HASH_MAP_INDEX_SIZE; i++)
		{
			if (!map->handle)
				return NULL;

			if (map->handle == handle)
			{
				if (mutex)
				{
					pthread_mutex_lock (&map->mutex);
					*mutex = &map->mutex;
				}
#ifdef  DEBUG
				if (i)
					fprintf (stderr, "found %lu after %i items\n",
							 (long unsigned int) handle, i);
#endif	/*DEBUG*/
				return (m_ItemSize <=
					(int) sizeof (map->data)) ? &map->data : map->data;
			}

			map++;
			if (map >= &m_Map[HASH_MAP_INDEX_SIZE])
				map = m_Map;
		};
#ifdef  DEBUG
		fprintf (stderr, "can't find %lu\n", (long unsigned int) handle);
#endif	 /*DEBUG*/
	}
	return NULL;
}

int
bmMapHandleToItem::GetItemCount (void)
{
	return m_MapIteratePos;
}

void *
bmMapHandleToItem::Add (bmHandle handle, pthread_mutex_t ** mutex)
{
	bmHandleMap *map;
	int i;

	if (m_ItemSize && handle)
	{

		map = HashMap (handle);

		for (i = 0; i < HASH_MAP_INDEX_SIZE; i++)
		{
			if (!map->handle)
			{
				pthread_mutex_init (&map->mutex, NULL);
				if (mutex)
				{
					pthread_mutex_lock (&map->mutex);
					*mutex = &map->mutex;
				}
				map->handle = handle;

				/* store object into m_MapIterate for quick interation */
				m_MapIterate[m_MapIteratePos++] = map;

				if (m_ItemSize <= (int) sizeof (map->data))
					return &map->data;
				else
				{
					map->data = malloc (m_ItemSize);
					if (m_ItemSize > (int) sizeof (map->data))
						memset (map->data, 0, m_ItemSize);
					return map->data;
				}
			}
			else if (map->handle == handle)
			{
				if (mutex)
				{
					pthread_mutex_lock (&map->mutex);
					*mutex = &map->mutex;
				}
				return (m_ItemSize <= (int) sizeof (map->data)) ? &map->data
					: map->data;
			}

			map++;
			if (map >= &m_Map[HASH_MAP_INDEX_SIZE])
				map = m_Map;
		}
	}
	return NULL;
}

int
bmMapHandleToItem::IterateLocked (bmIterationCallback cb, double timestamp,
								  bool realtime)
{
	int count;
	bmHandleMap **p, *map;

	if (cb && m_ItemSize)
	{
		p = m_MapIterate;
		count = m_MapIteratePos;
		while (count--)
		{
			map = *p++;
			pthread_mutex_lock (&map->mutex);
			cb ((m_ItemSize <= (int) sizeof (map->data)) ? &map->data
				: map->data, timestamp, realtime);
			pthread_mutex_unlock (&map->mutex);
		}
		map++;
		return m_MapIteratePos;
	}
	else
		return -1;

}
